MHMADYHYA/smart-neighborhood-power-system-design/docs/Stage_0_Understanding_Report.md

# Stage 0 — דוח הבנה וסיווג מקורות (סופי)
**תאריך:** 11/06/2026 · בוצע לפני תחילת העריכה, כנדרש.

## מהות הפרויקט
תיק תכנון סופי (אבן דרך רביעית — דוח מסכם) למערכת חשמל במתח נמוך לשכונת מגורים חכמה, מסווג **אפשרות ב׳** לפי הנחיות רשם המהנדסים: 3 בניינים (A/B/C) × 15 קומות (קרקע טכנית + 14 מגורים × 4 דירות) = **168 דירות** בחיבור 3×25A; הזנה 22kV דרך **2×1000kVA** (יבשים, Dyn11, uk≈6%) אל **MDB דו-מקטעי 2500A / Icw 65kA** (2×ACB 1600A + Bus-tie); **PV 200kWp**, **BESS 250kW/500kWh**, **30×11kW EV + DLM**, **גנרטור 300kVA + ATS**, **UPS 20kVA/8.75kWh**, **קבלים 200kvar detuned**, **EMS/BMS**, הארקת **TN-S**, חלוקה תת-קרקעית. ביקוש: 1,312.7 / 1,603.7kVA → העמסה 65.6% / 80.2%.

## קבצים שנמצאו, תפקידם ומה נעשה בהם
| קובץ / קבוצה | סיווג | שימוש |
|---|---|---|
| `Downloads\...מתוקן(2).docx` (11/06 13:11) | **דוח הבסיס** — תוכן אבן-דרך-3 לאחר תיקוני "סאלח" (574A, BESS Ir=380, ציבורי 23A/32A/4×10, AN, טבלת IEE) | מקור התוכן היחיד; חולץ ברמת בלוקים כולל משוואות OMML |
| `הנחיות משרד העבודה...23-02-2026.pdf` (+`_extracted\ministry.txt`) | דרישות מחייבות — רשם המהנדסים | בסיס טבלת ההתאמה (27 דרישות) בפרק 2 |
| `מדריך פרויקטים...04-26.pdf` (+`guide.txt`) | מגדיר את דרישות אבן הדרך הרביעית (דוח מסכם + שרטוטי חובה + פוסטר) | בסיס מיפוי הדרישות; הפוסטר מוגש בנפרד |
| `חוק החשמל 2017.pdf` | בסיס חוקי | סעיפי "התאמה לחוק" בכל פרק — עקרונות בלבד, ללא ציטוט מספרי סעיפים |
| IEC-60909.pdf, Electrodynamic forces, כוונון הגנות שניידר, קטלוגי Schneider/ABB/Eaton/Legrand, תקציר 4000 | מקורות טכניים/קטלוגיים | תיעוד בטבלת מקורות; ללא צילומי קטלוג בגוף הדוח (לפי ההנחיות) |
| `05_final_word\` + `_milestone3_build\` | תשתית בנייה קודמת (Word COM RTL, מחוללי שרטוטים) | אומצה והורחבה (build4, drawings_final) |
| `מקרא.dwg`, `תכנון לוחות חשמל.dwg`, `סכימת זרמי קצר+מפלי מתח.dwg` | קבצי AutoCAD מקוריים של הסטודנט | צורפו לחבילה (`_drawings_final\DWG_original`) ונרשמו בנספח L |
| `אמיר וסלאח.pdf`, `עודד ונמרוד.pdf`, תבניות אבן דרך, `אבן דרך שנייה.docx`, `11/222/3/4/5A.pdf` (הרצאות) | ייחוס סגנוני / רקע קורס | לא הועתק מהם תוכן |
| `01/02_*.txt` (פרומפטים ישנים), `_build\`, `CHANGELOG` | היסטוריית עבודה | לא בשימוש — הוחלפו בהנחיות הנוכחיות |

## סתירות וערכים ישנים שאותרו (ותוקנו)
1. **זהות** — הקובץ נשא ניסוחי "דוח ביניים – אבן דרך שלישית" בשער, בתקציר, בפרק 2, בפרק 20 ובעשרות פסקאות ("ראשוני", "יושלם בדוח הסופי").
2. **UPS הפוך** — במסמך 8.75kVA/20kWh; הנתון המחייב: **20kVA/8.75kWh** → חושבו מחדש מזין (MCB 40A, 4×10), Ik (3.4kA) וזמן גיבוי (≈1.1h).
3. **סתירה פנימית בפרק 9** — חישוב 9.1 השתמש ב-490A/MCCB 630/"2×5×240" מול 574A/800A/2×(4×300) בשאר הדוח.
4. **"4×35" שרד** בטבלת מפל המתח (רייזר) בסתירה ל-9.7 → מודל הרייזר תוקן ו-ΔU מצטבר עודכן 4.0%→3.5%.
5. **Icu של ACB** — 50kA בחלק מהטבלאות מול 65kA באחרות → אוחד ל-65/65kA.
6. **לוח קומה** — 125A/10kA/80A בלתי עקביים → אוחד ל-MCCB 80A, Icu 25kA.
7. **Ik ללוח ציבורי/UPS** (11/10kA) לא תאם לכבל 4×10 → חושב מחדש 3.4kA.
8. **שרטוטים ישנים** הציגו UPS 8.75kVA, PUBLIC 100A, 50kA → הופקו מחדש.
9. **חוסרים מול דרישות הדוח המסכם** — אין פרק חלופות, אין BOQ סופי, נספחים חלקיים (חסרים C/I/J/M), אין טבלאות התאמה מלאות, אין Ik,min לכל לוח, תהודת פסים "תושלם" — הכל הושלם.

## איך נבדקה ההתאמה לחוק החשמל ותקנות החשמל
לכל נושא תכן הוצגה שרשרת ההוכחה המעשית (Ib → In/Ir → Iz′ → I2≤1.45Iz′ → ΔU → Ik max/min → Icu/Ics → שיטת הגנה/הארקה → החלטה), בתוספת: טבלת התאמה לפי 16 נושאי תכנון (פרק 2), סעיף ייעודי בכל פרק הנדסי, ושתי טבלאות בקרה בפרק 22. בהיעדר ציטוט נוסח מחייב — הניסוח "בהתאם לעקרונות חוק החשמל ותקנות החשמל בנושא..." בלבד, ללא המצאת מספרי סעיפים.

## החלטת ביצוע
התוכן ההנדסי בבסיס נמצא איכותי ועקבי ברובו; הביצוע התמקד ב: (א) הסבת הזהות לדוח מסכם; (ב) השלמת הפרקים/נספחים/טבלאות הנדרשים; (ג) תיקון הסתירות שלעיל; (ד) הפקת שרטוטים סופיים תואמי-ערכים והטמעתם; (ה) בקרת איכות ממוכנת. כל המספרים הקבועים של הפרויקט נשמרו ללא שינוי.
