MHMADYHYA/smart-neighborhood-power-system-design/docs/source_manifest.md

# Source Manifest

- Local source: `C:\Users\mhmad\OneDrive\Desktop\סוף כנרת_final_submission\דוח מסכם - אבן דרך רביעית - תכנון שכונת מגורים חכמה - סופי.docx`

Raw reports with student IDs or private information were intentionally not copied into this public-ready repository.
