MHMADYHYA/smart-neighborhood-power-system-design/assets/full_report_media/report_media_002.png

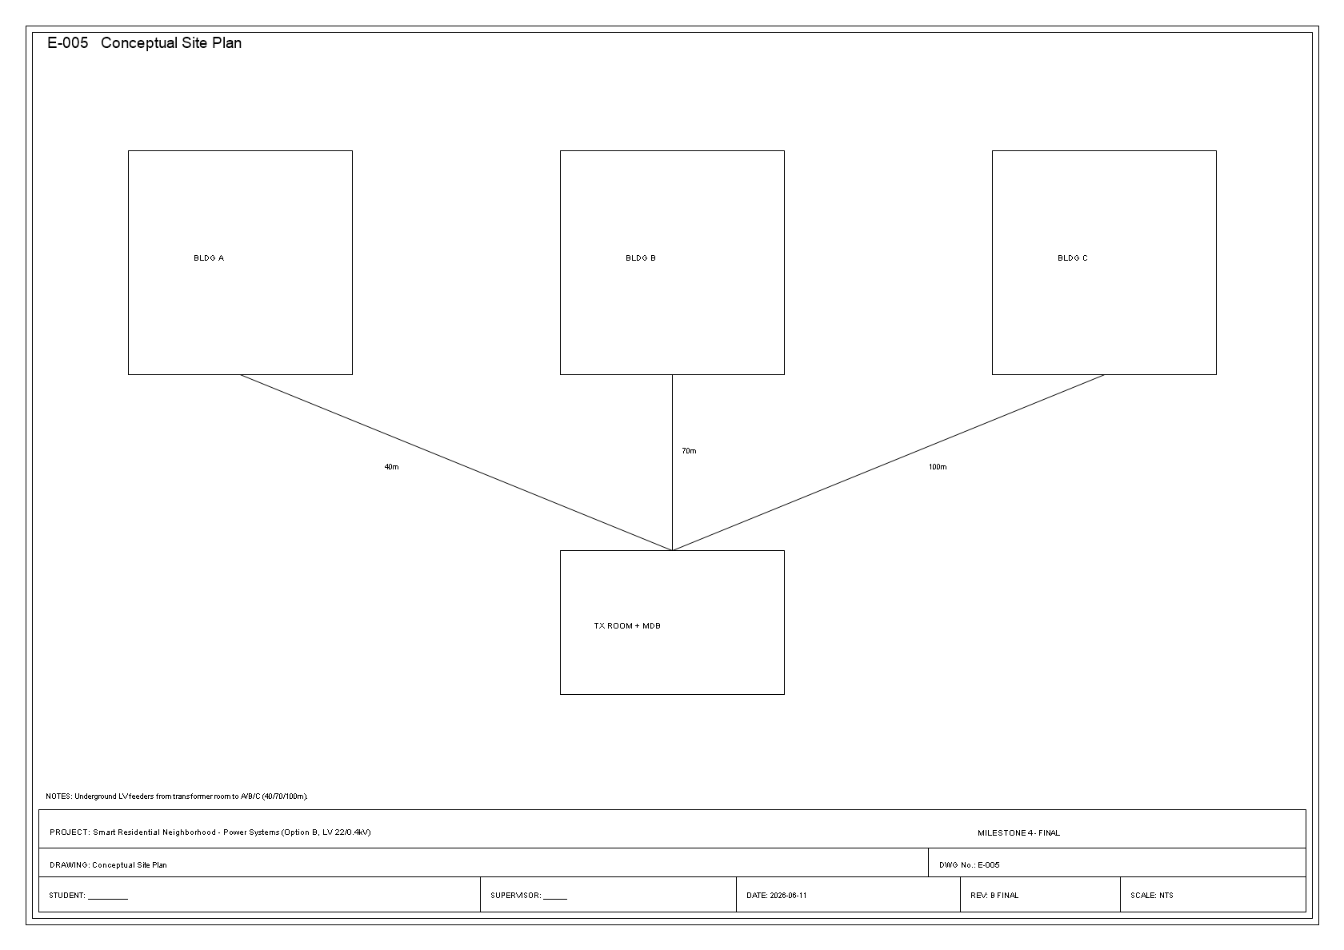
assets/full_report_media/report_media_002.png
