MHMADYHYA/smart-neighborhood-power-system-design/assets/rendered_report_pages/דוח_מסכם_-_אבן_דרך_רביעית_-_תכנון_שכונת_מגורים_חכמה_-_סופי-004.png

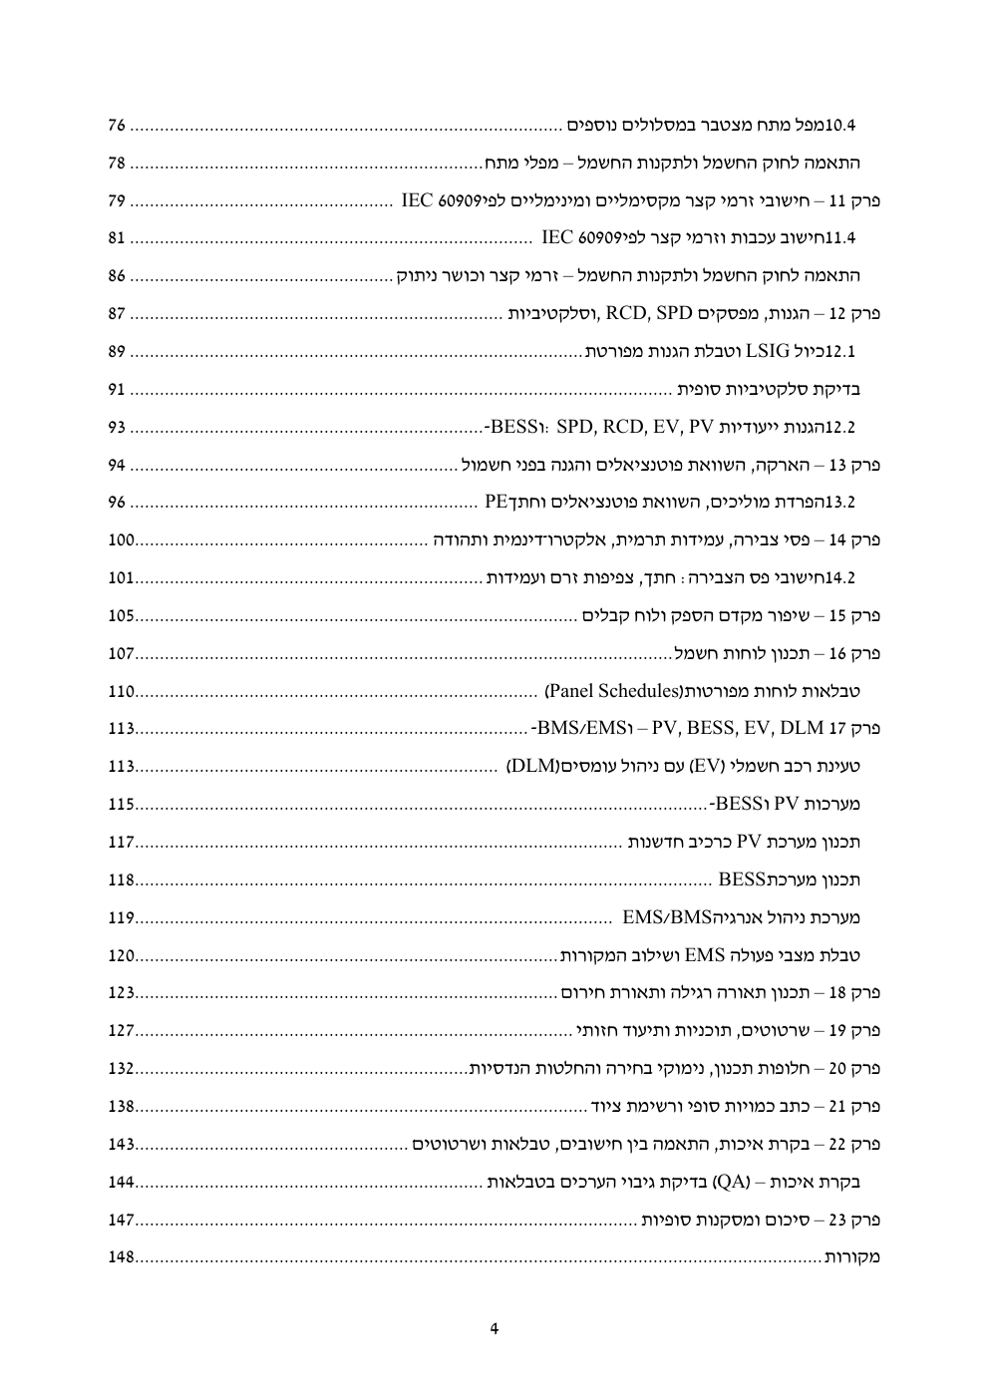
assets/rendered_report_pages/דוח_מסכם_-_אבן_דרך_רביעית_-_תכנון_שכונת_מגורים_חכמה_-_סופי-004.png
