MHMADYHYA/smart-neighborhood-power-system-design/engineering_drawings/E-001_Main_SLD_Neighborhood.png

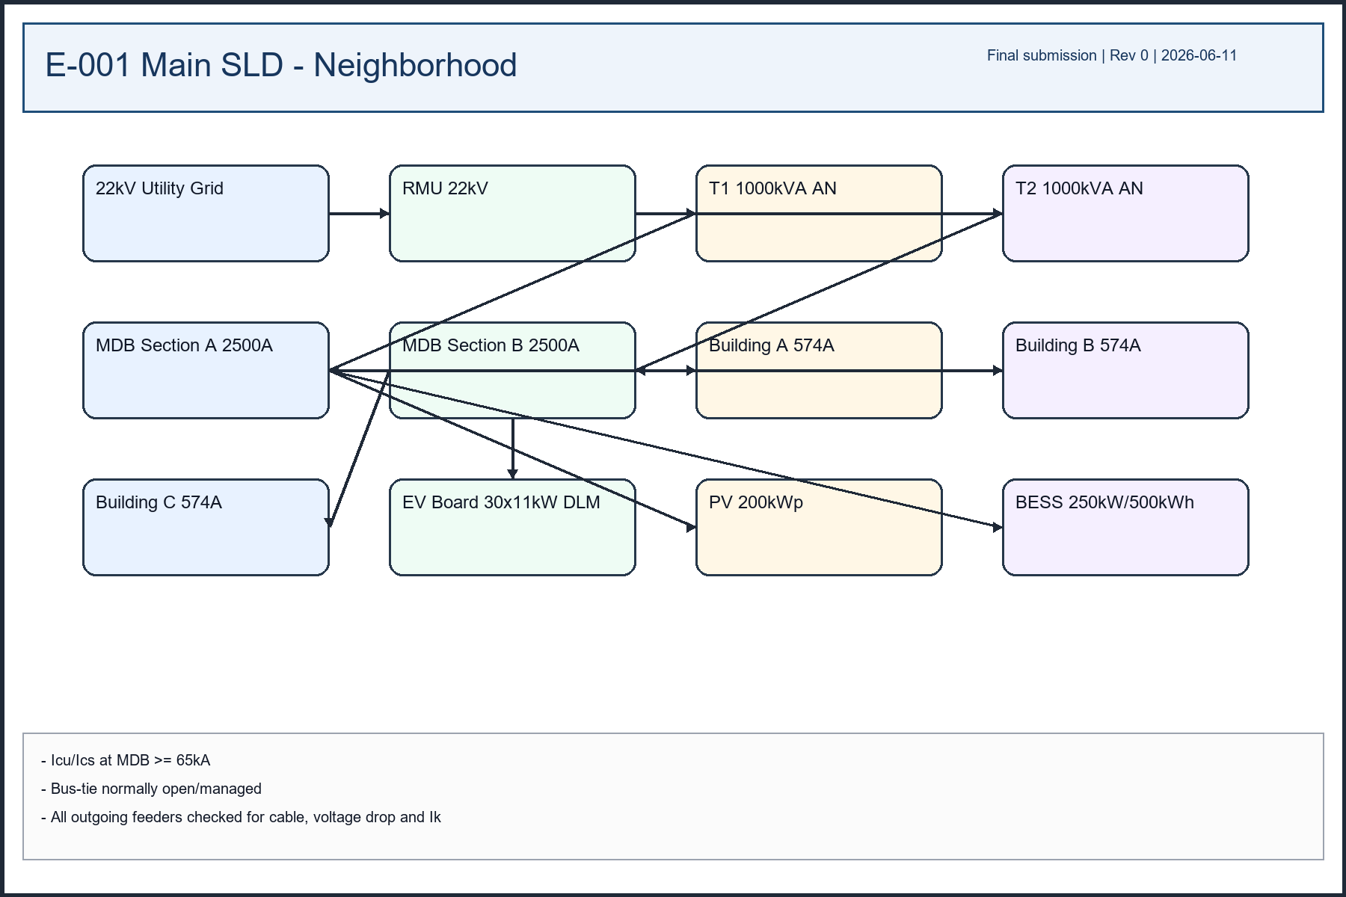
engineering_drawings/E-001_Main_SLD_Neighborhood.png
