MHMADYHYA/smart-neighborhood-power-system-design/engineering_drawings/E-004_Sub_Panels_Layout.png

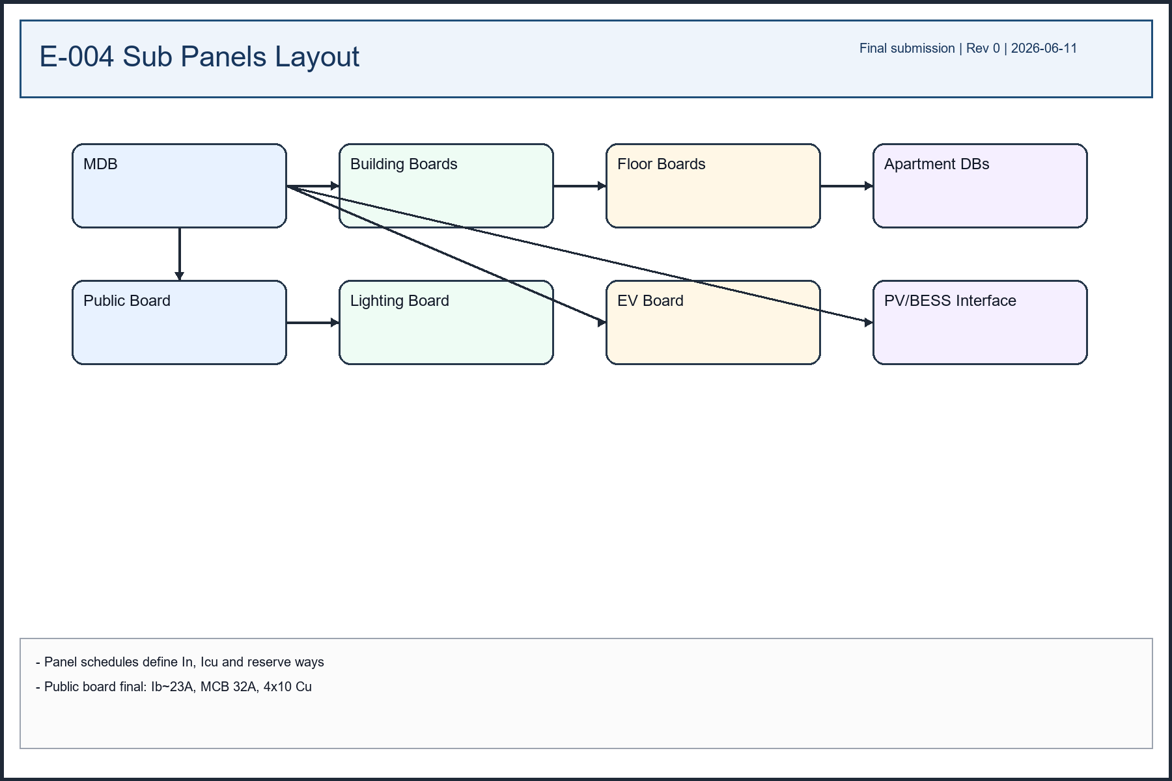
engineering_drawings/E-004_Sub_Panels_Layout.png
