MHMADYHYA/smart-neighborhood-power-system-design/engineering_drawings/E-005_Conceptual_Site_Plan.png

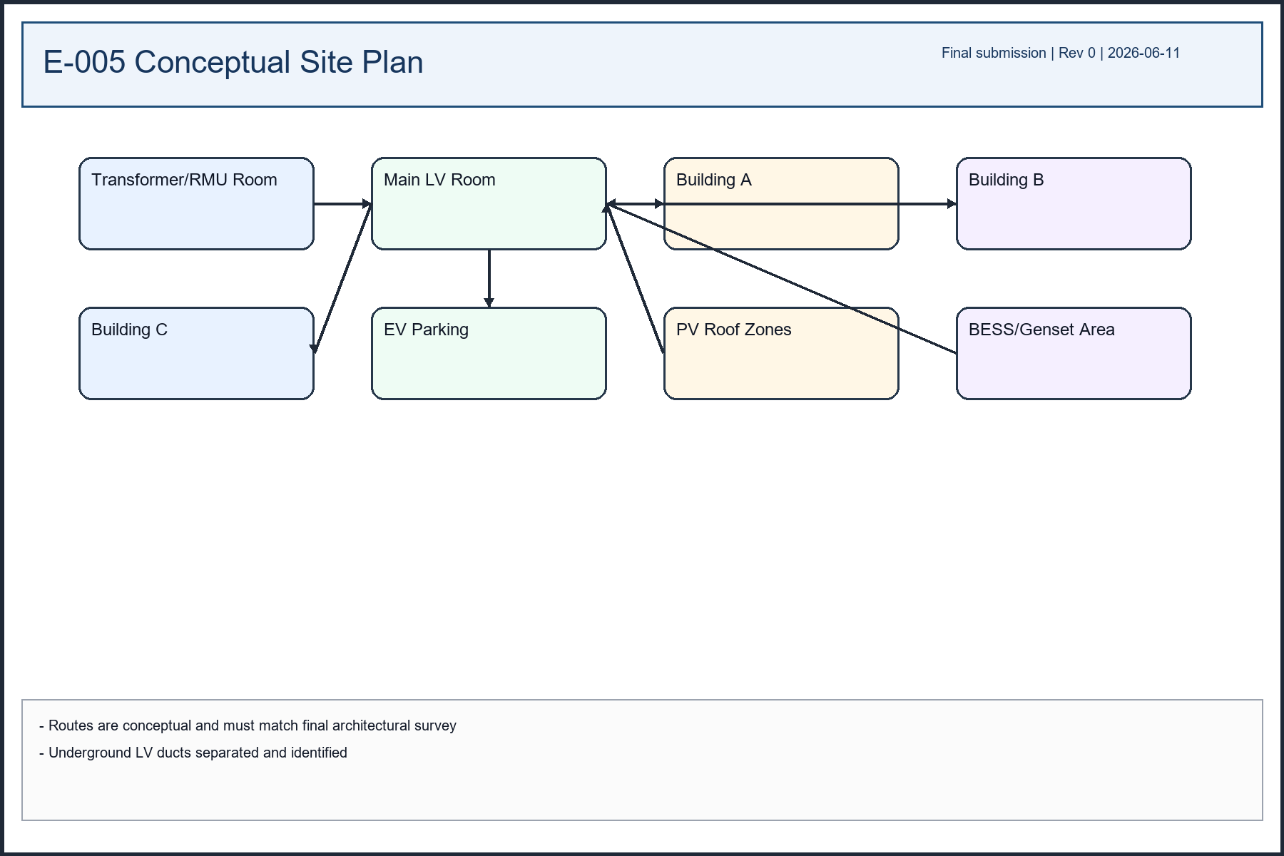
engineering_drawings/E-005_Conceptual_Site_Plan.png
