MHMADYHYA/smart-neighborhood-power-system-design/engineering_drawings/E-006_Underground_Cable_Routing.png

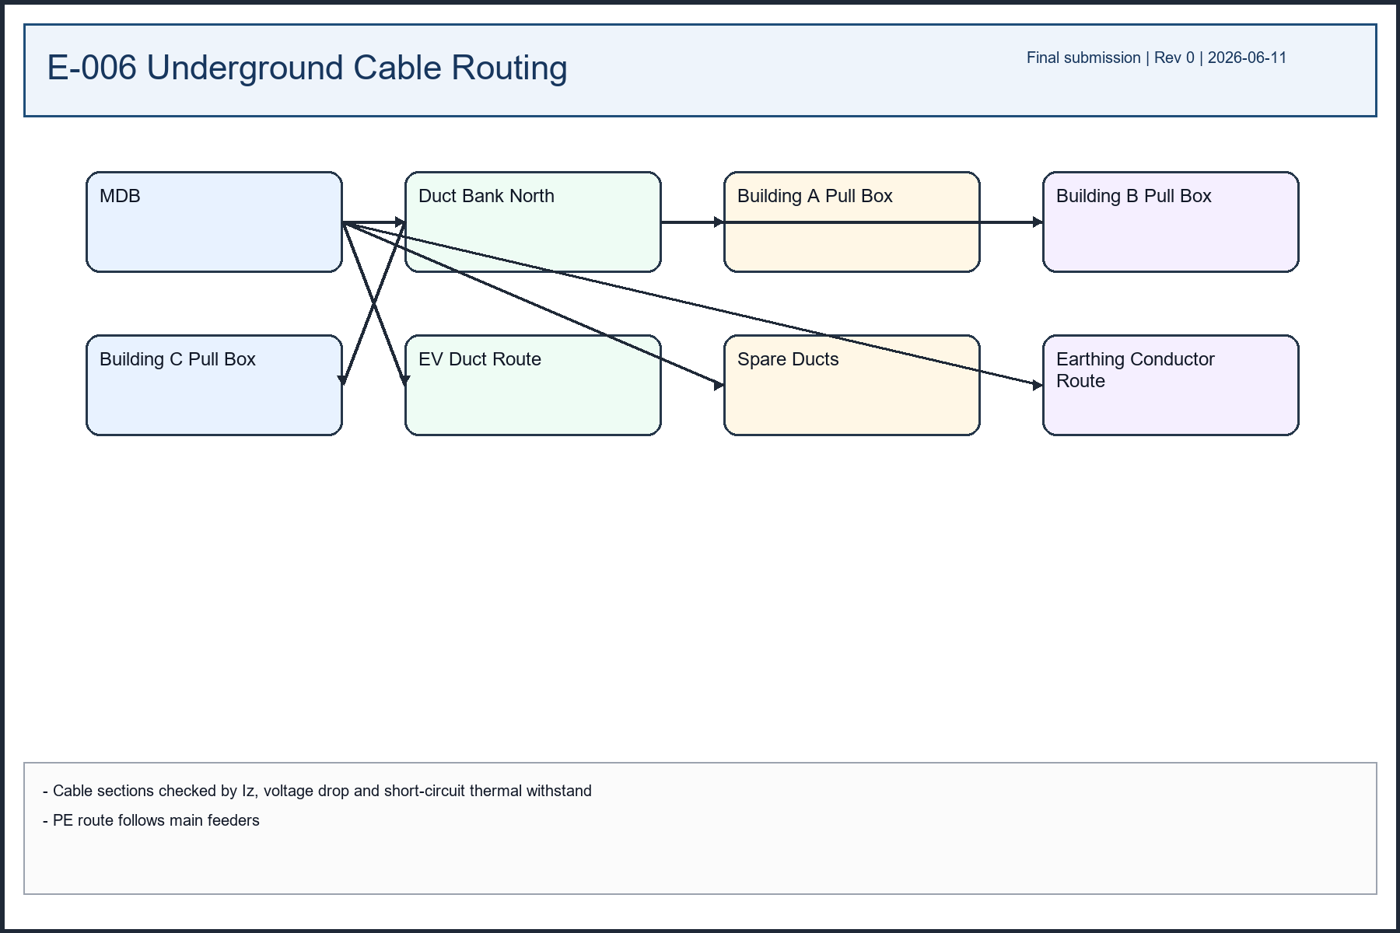
engineering_drawings/E-006_Underground_Cable_Routing.png
