MHMADYHYA/smart-neighborhood-power-system-design/engineering_drawings/E-007_Transformer_RMU_Room.png

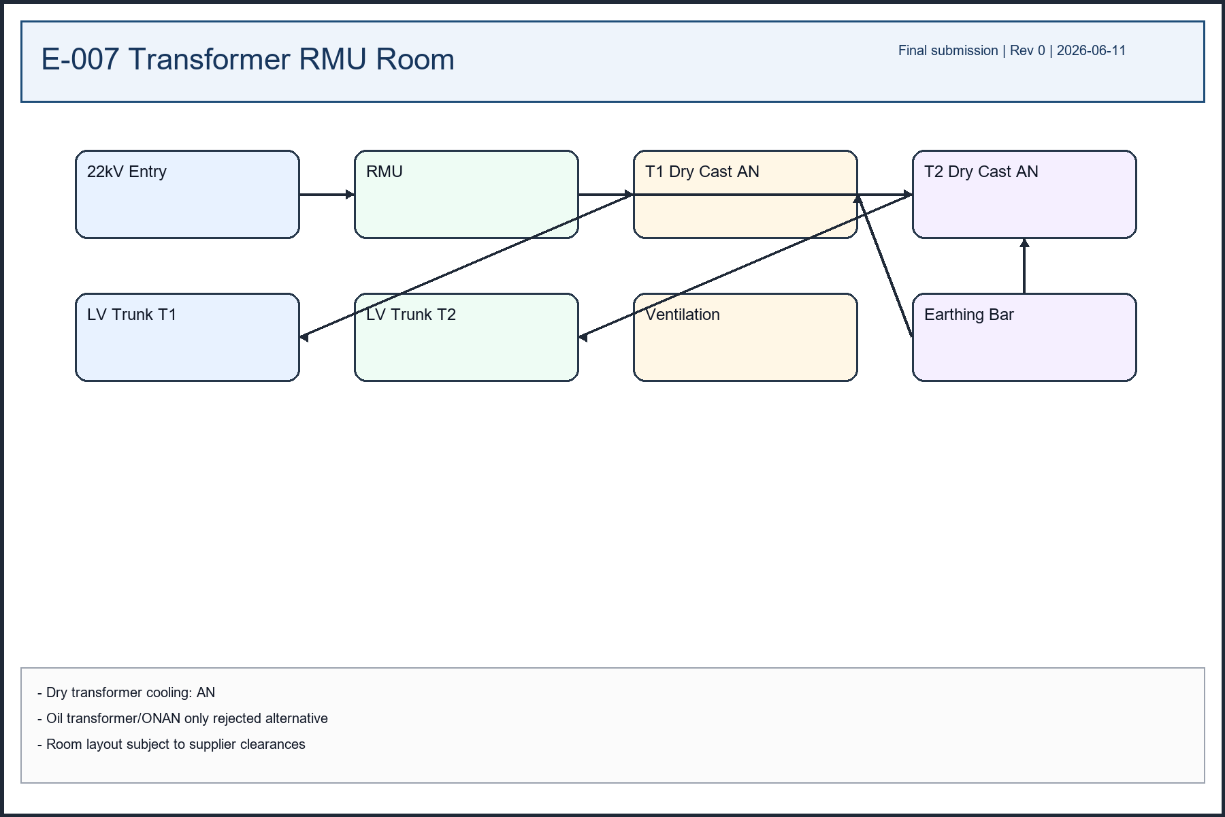
engineering_drawings/E-007_Transformer_RMU_Room.png
