MHMADYHYA/smart-neighborhood-power-system-design/engineering_drawings/E-008_Generator_ATS_UPS_SLD.png

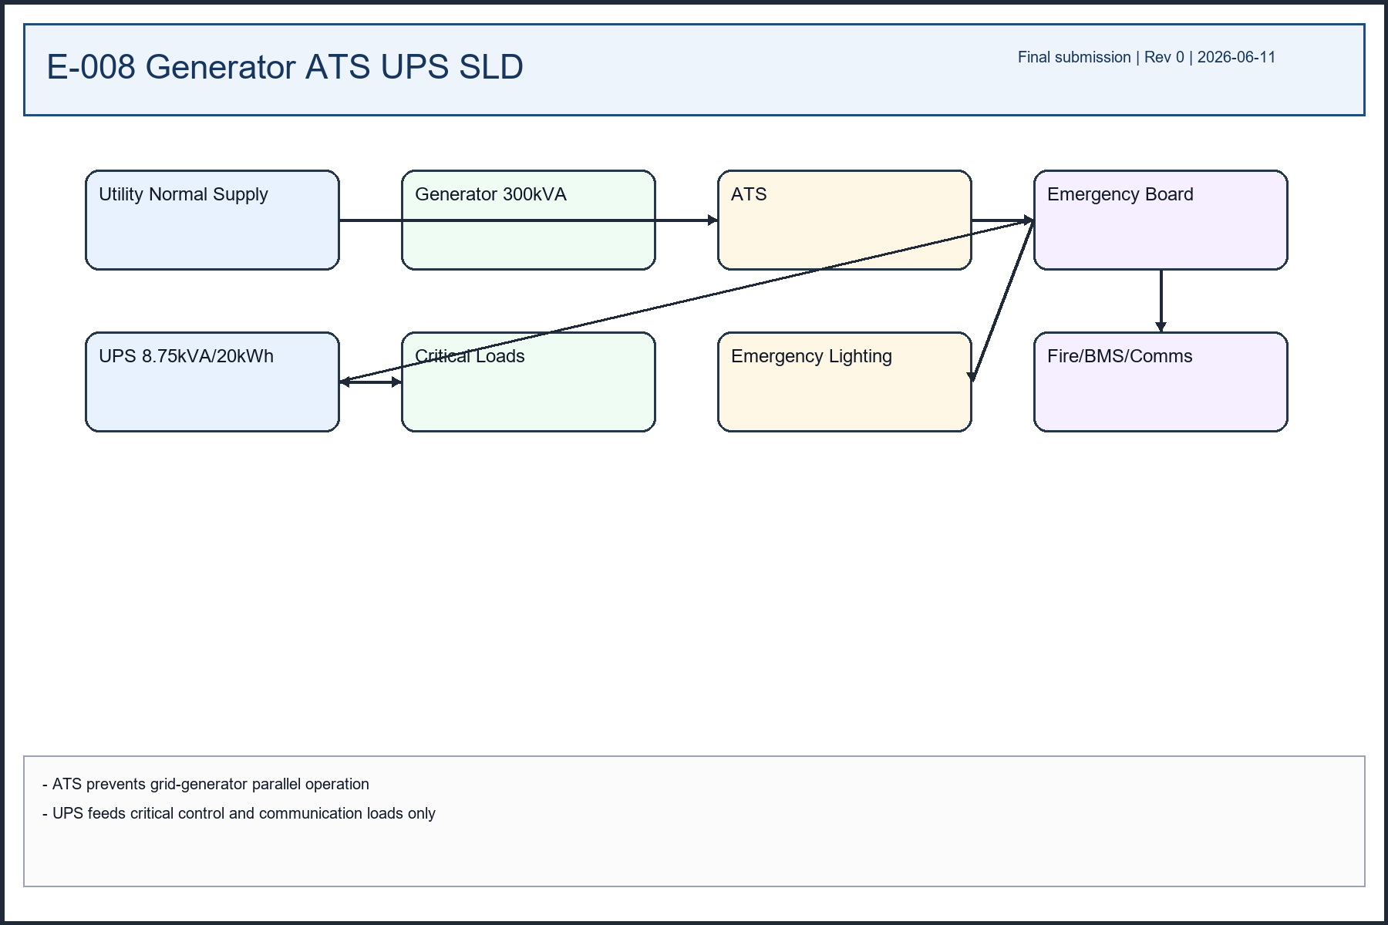
engineering_drawings/E-008_Generator_ATS_UPS_SLD.png
