MHMADYHYA/smart-neighborhood-power-system-design/engineering_drawings/E-009_PV_BESS_EV_SLD.png

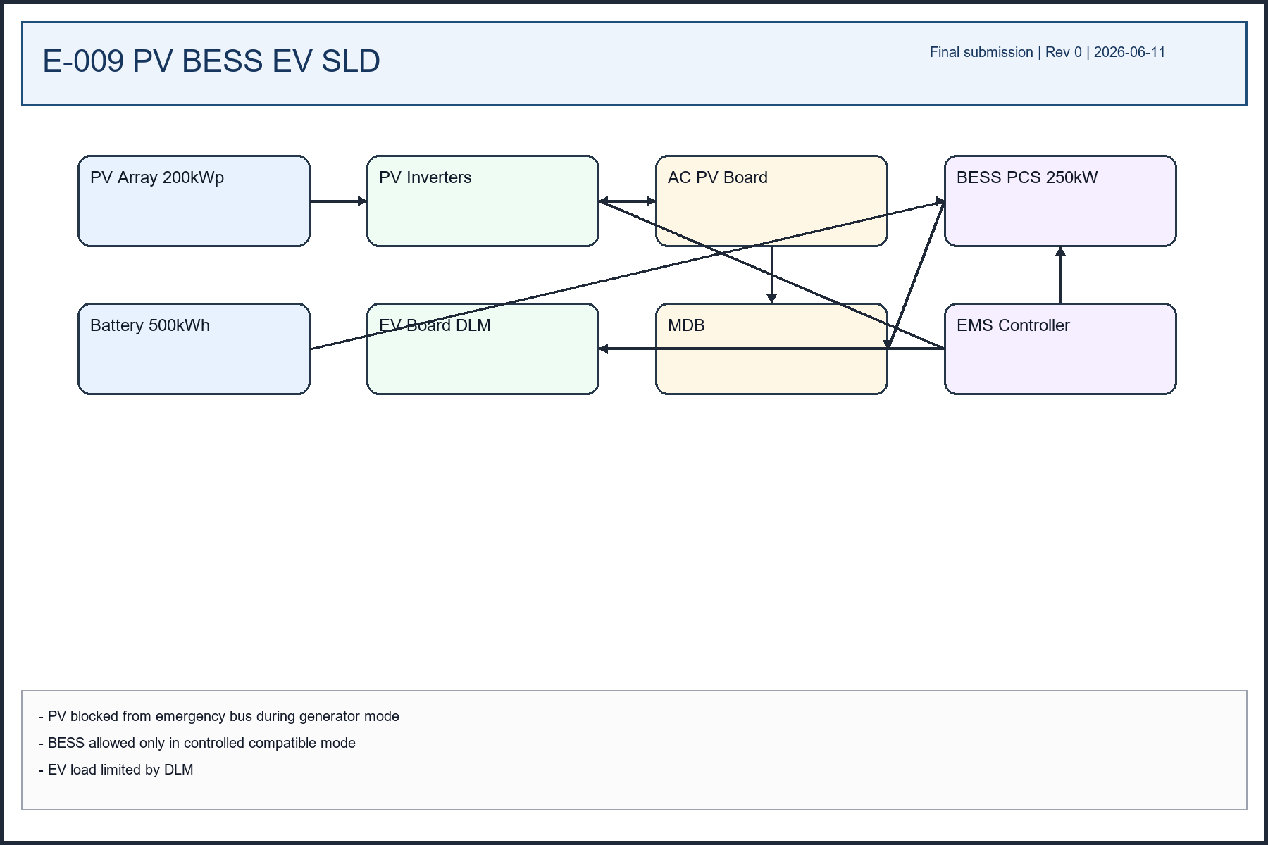
engineering_drawings/E-009_PV_BESS_EV_SLD.png
