MHMADYHYA/smart-neighborhood-power-system-design/engineering_drawings/E-010_Earthing_and_Bonding.png

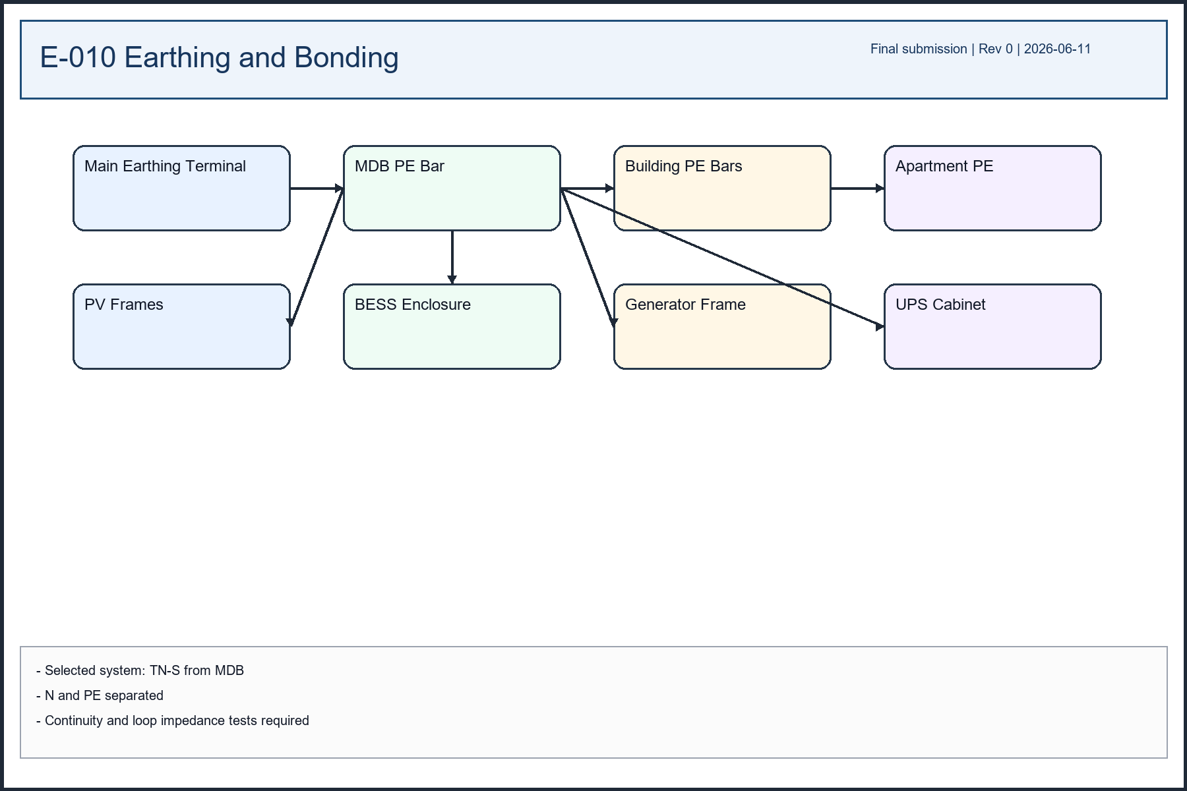
engineering_drawings/E-010_Earthing_and_Bonding.png
