MHMADYHYA/smart-neighborhood-power-system-design/engineering_drawings/E-011_Protection_Selectivity.png

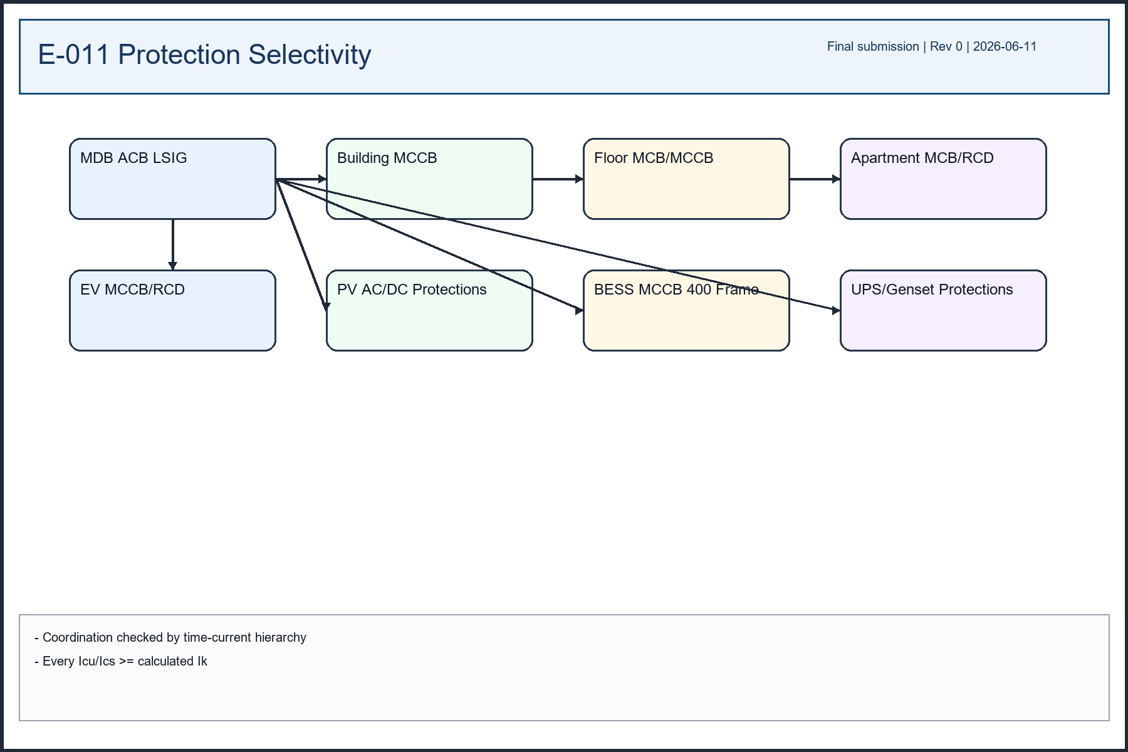
engineering_drawings/E-011_Protection_Selectivity.png
