MHMADYHYA/smart-neighborhood-power-system-design/engineering_drawings/E-012_BMS_EMS_Architecture.png

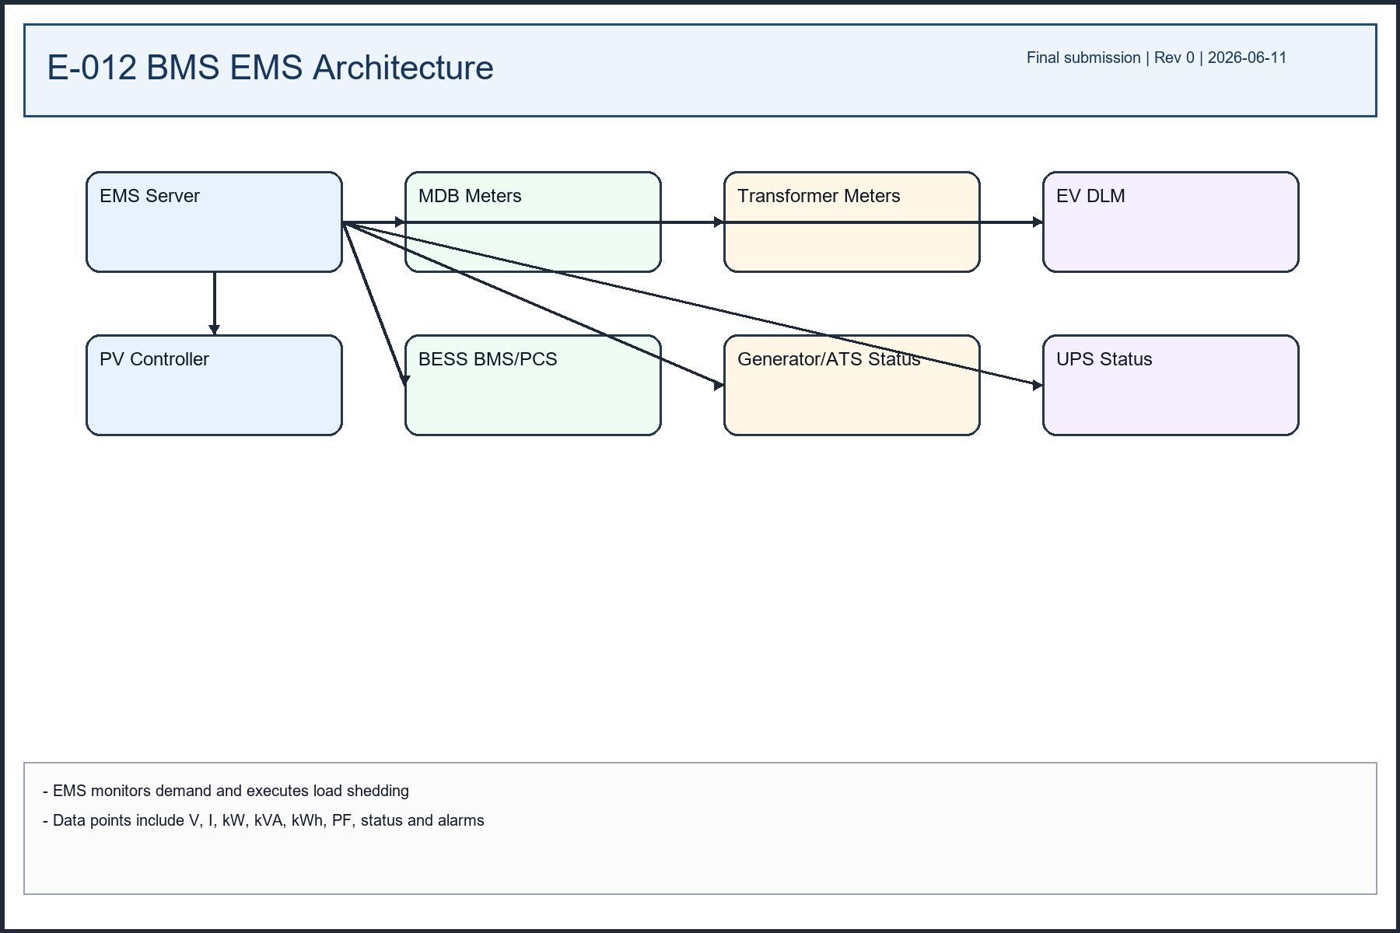
engineering_drawings/E-012_BMS_EMS_Architecture.png
