MHMADYHYA/smart-neighborhood-power-system-design/engineering_drawings/E-013_Lighting_and_Emergency_Lighting.png

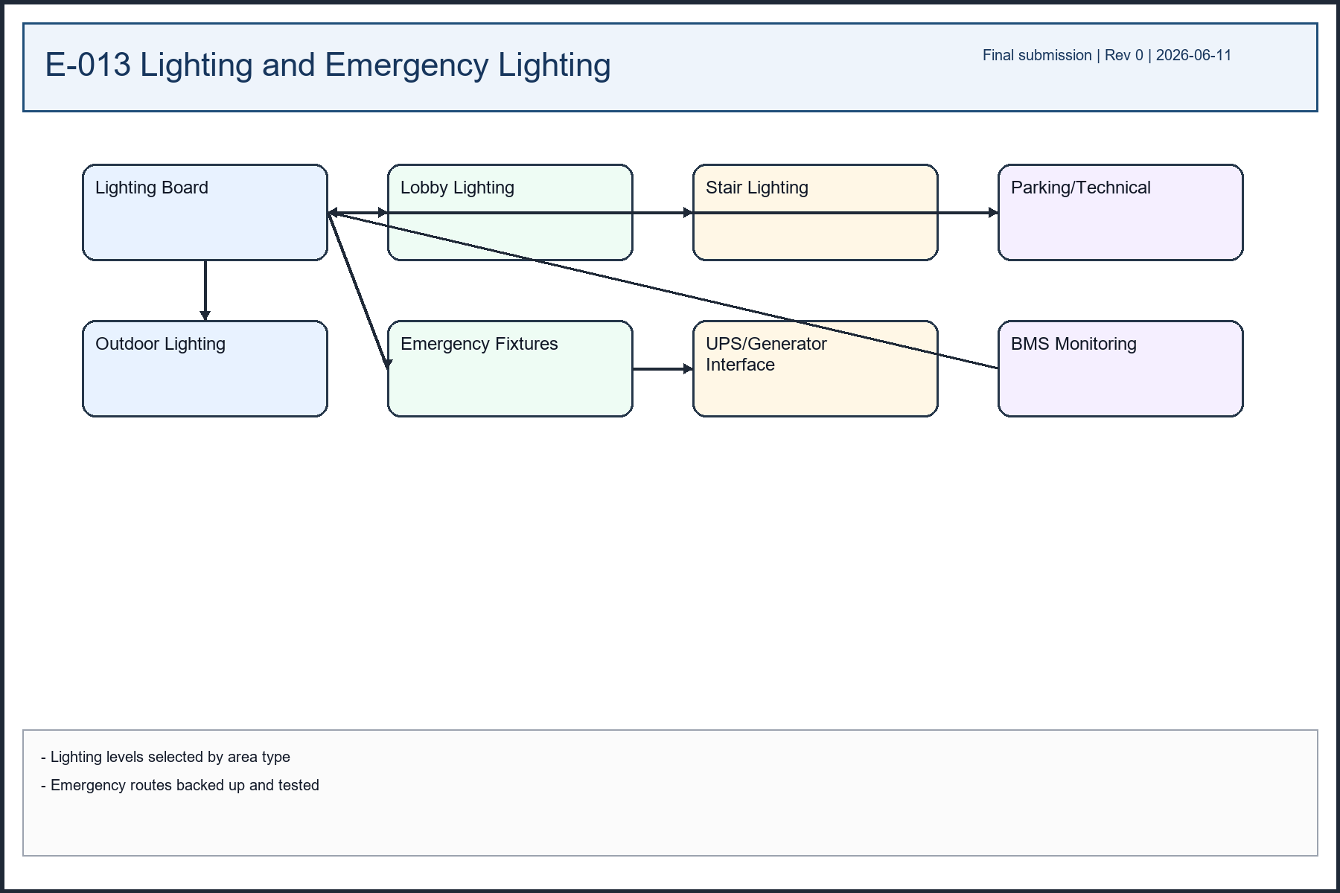
engineering_drawings/E-013_Lighting_and_Emergency_Lighting.png
