MHMADYHYA/smart-neighborhood-power-system-design/engineering_drawings/E-014_Final_Coordination_Drawing.png

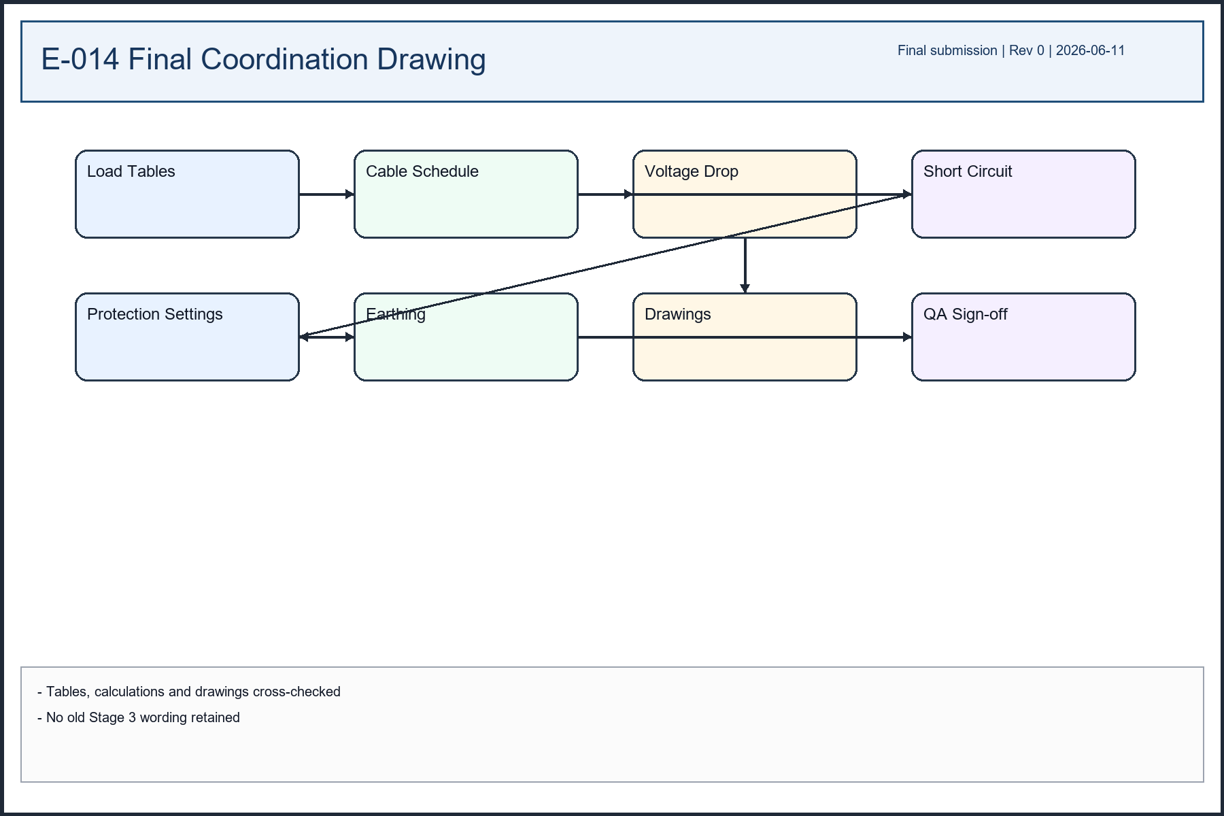
engineering_drawings/E-014_Final_Coordination_Drawing.png
