MHMADYHYA/smart-neighborhood-power-system-design/engineering_drawings/E-015_Normal_LV_Distribution_View.png

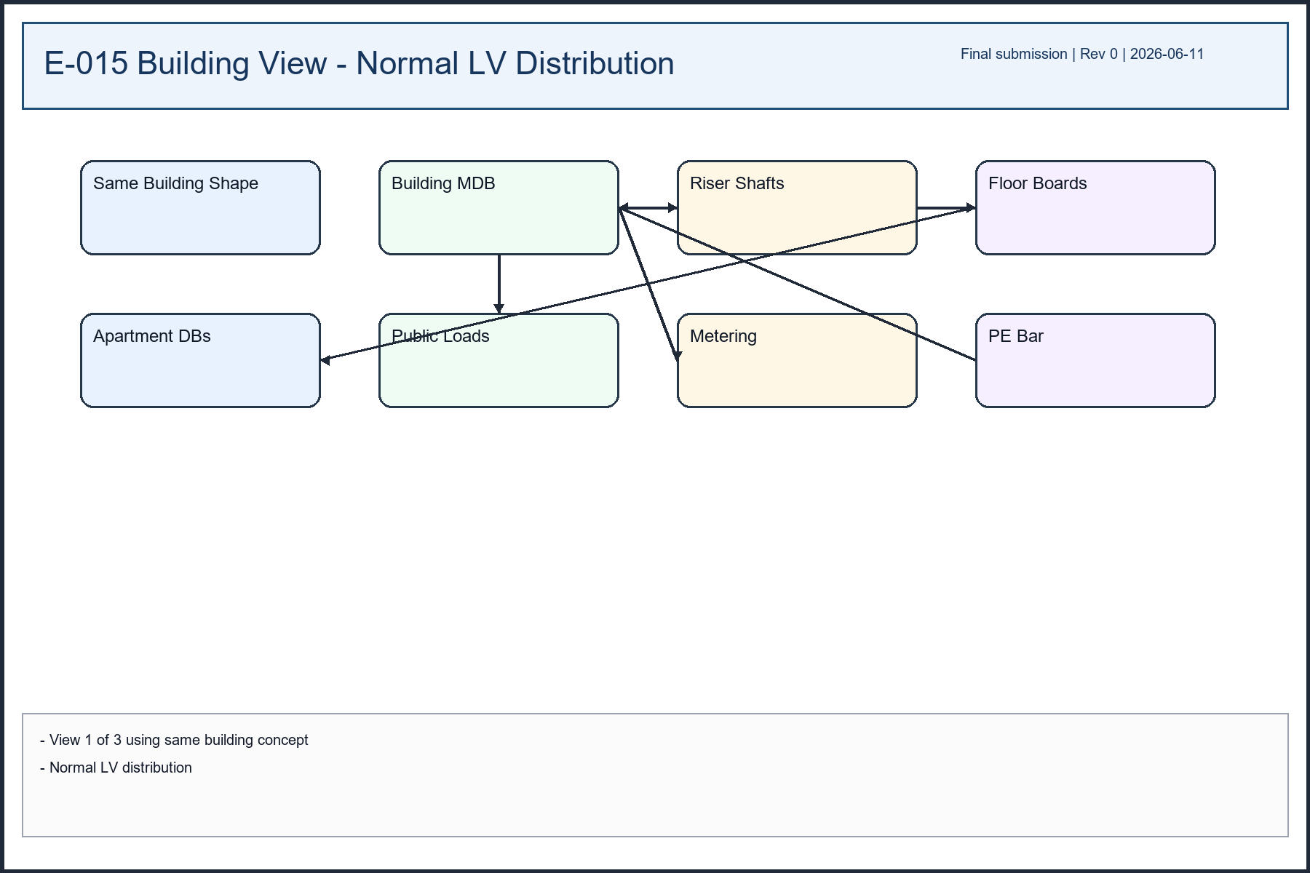
engineering_drawings/E-015_Normal_LV_Distribution_View.png
