MHMADYHYA/smart-neighborhood-power-system-design/engineering_drawings/E-017_Earthing_Bonding_View.png

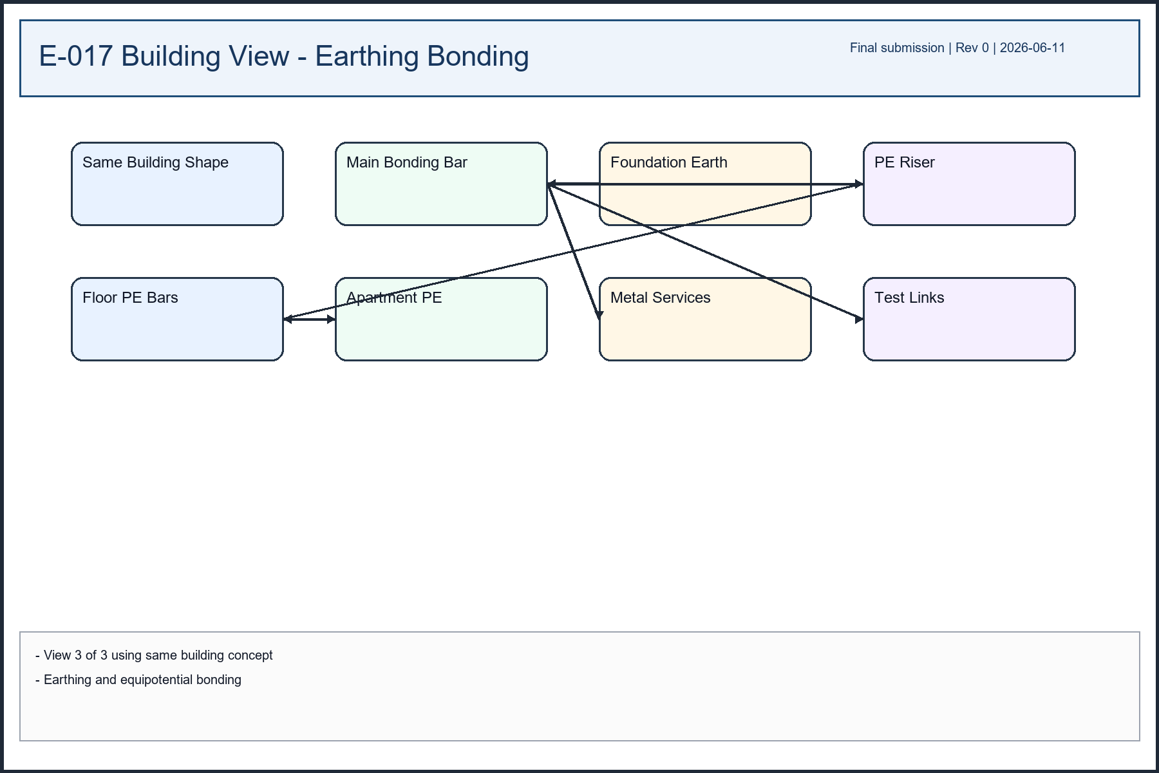
engineering_drawings/E-017_Earthing_Bonding_View.png
