MHMADYHYA/smart-neighborhood-power-system-design/engineering_drawings/PNG/E-003_Main_LV_MDB_Layout.png

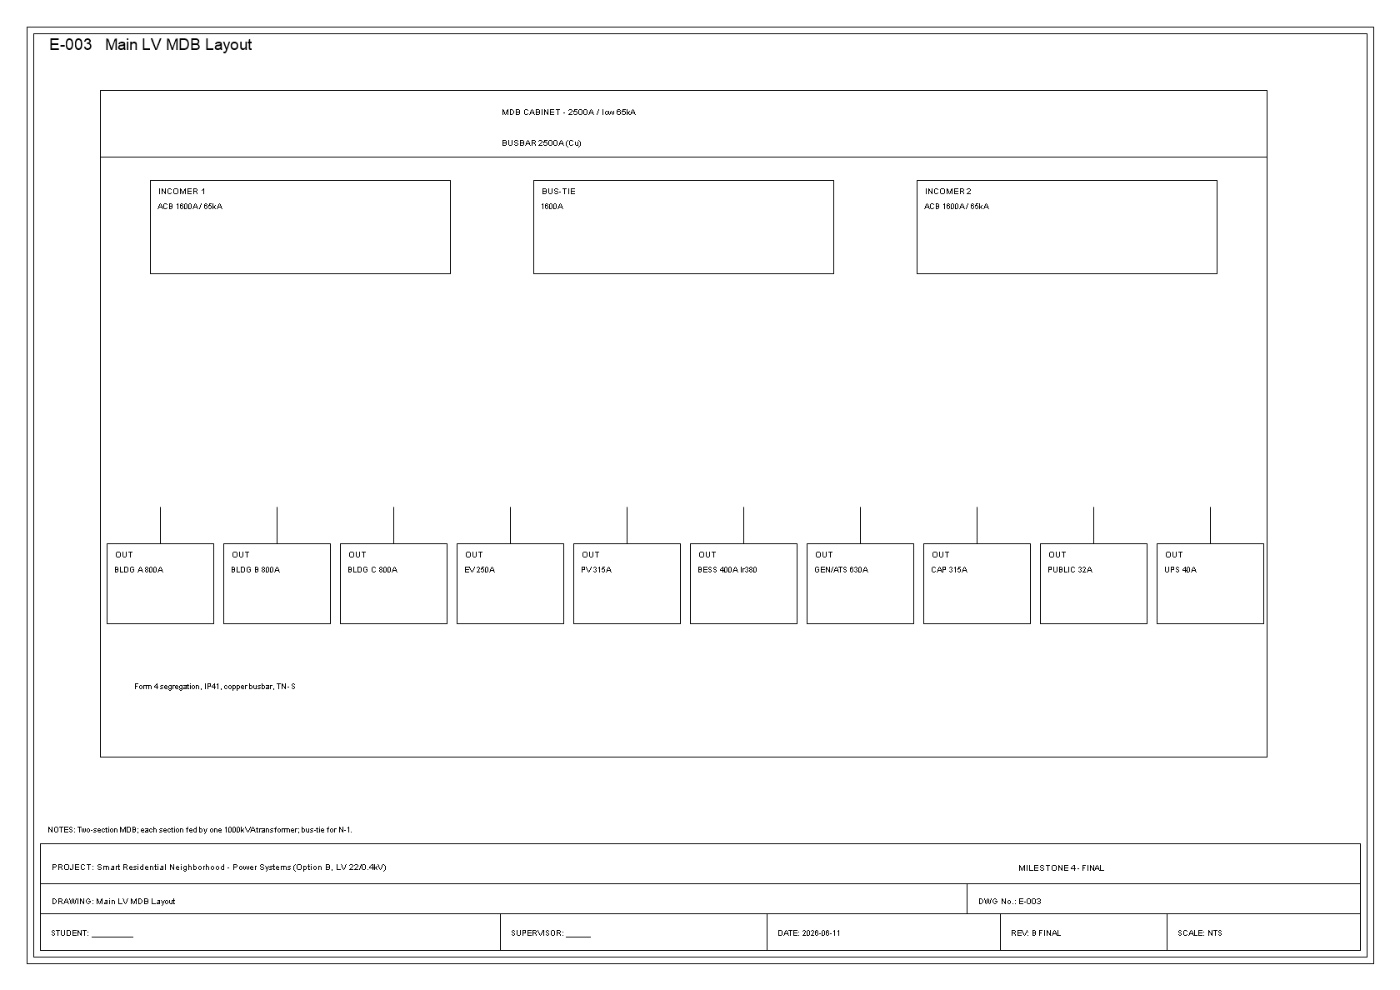
engineering_drawings/PNG/E-003_Main_LV_MDB_Layout.png
