MHMADYHYA/smart-neighborhood-power-system-design/engineering_drawings/PNG/E-006_Underground_Cable_Routes.png

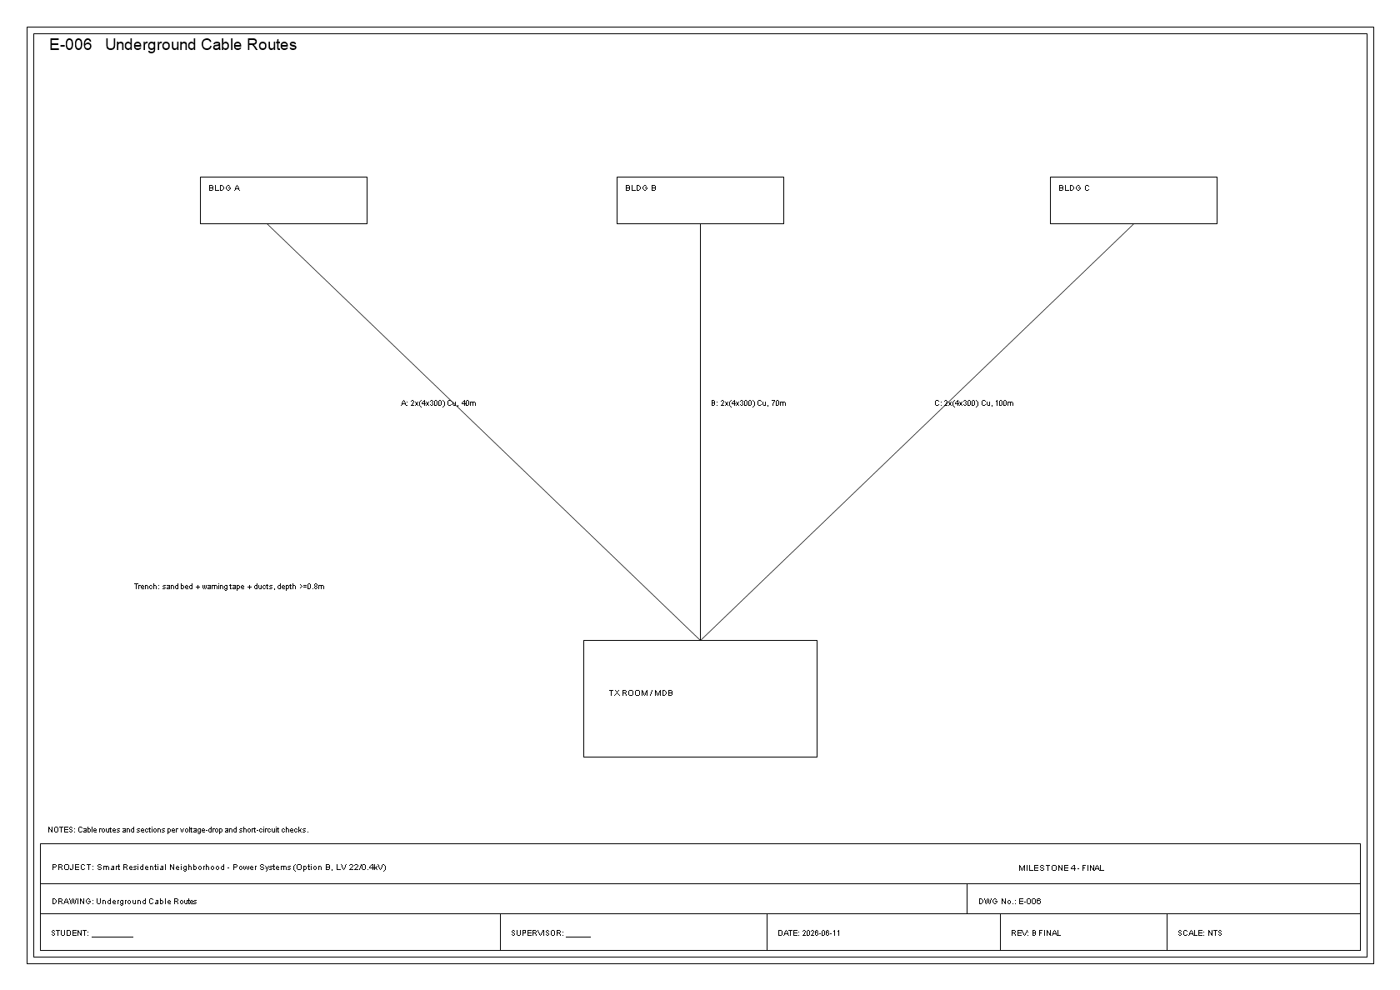
engineering_drawings/PNG/E-006_Underground_Cable_Routes.png
