MHMADYHYA/smart-neighborhood-power-system-design/engineering_drawings/PNG/E-007_Transformer_Room_Layout.png

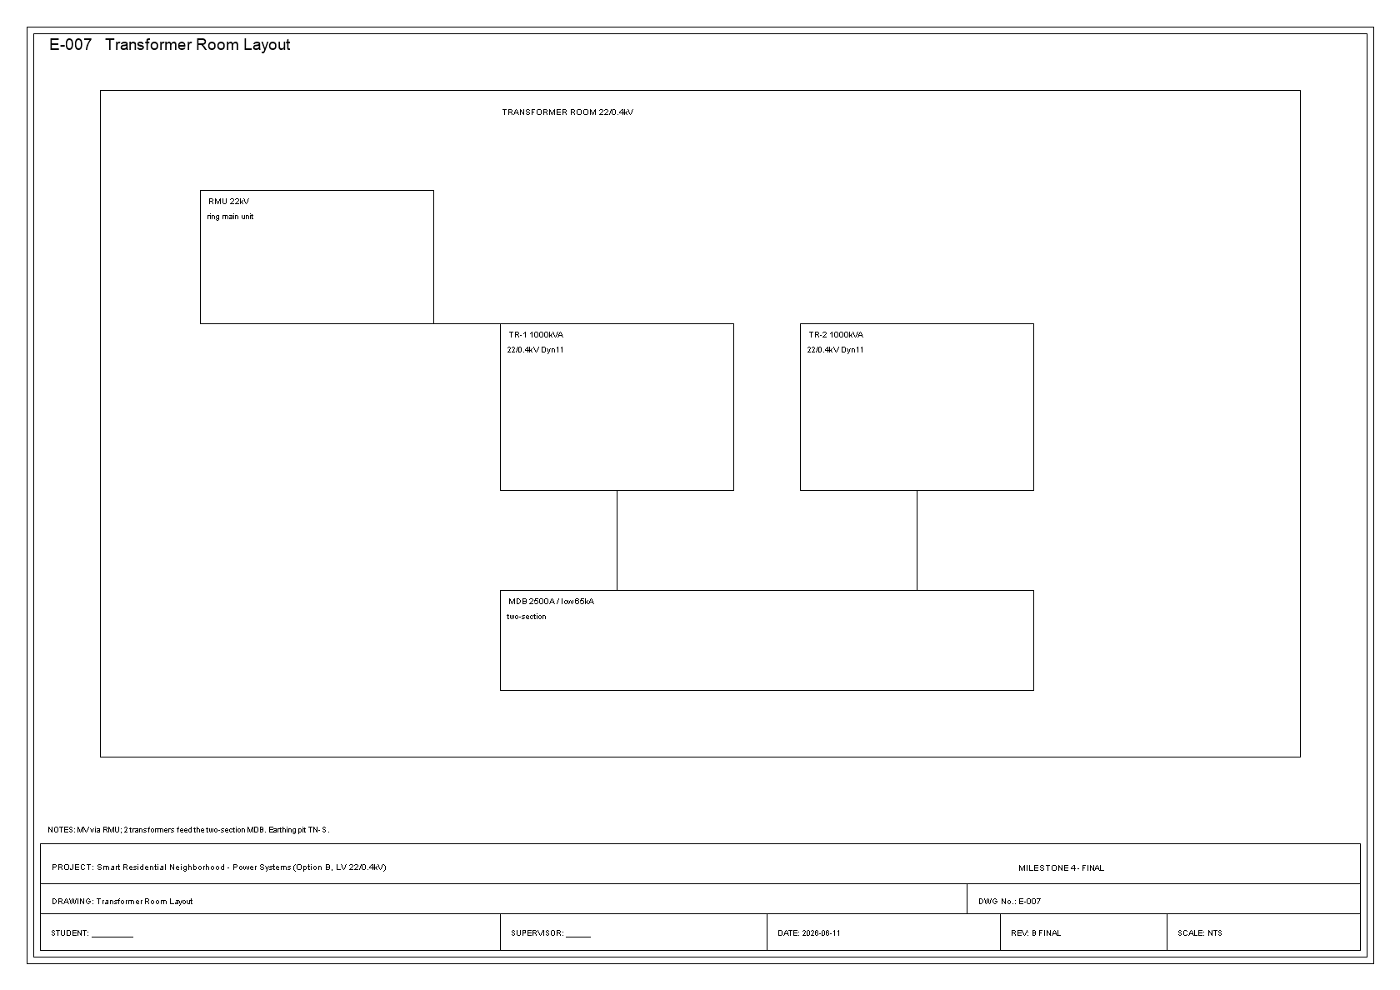
engineering_drawings/PNG/E-007_Transformer_Room_Layout.png
