MHMADYHYA/smart-neighborhood-power-system-design/engineering_drawings/PNG/E-012_EMS_BMS_Architecture.png

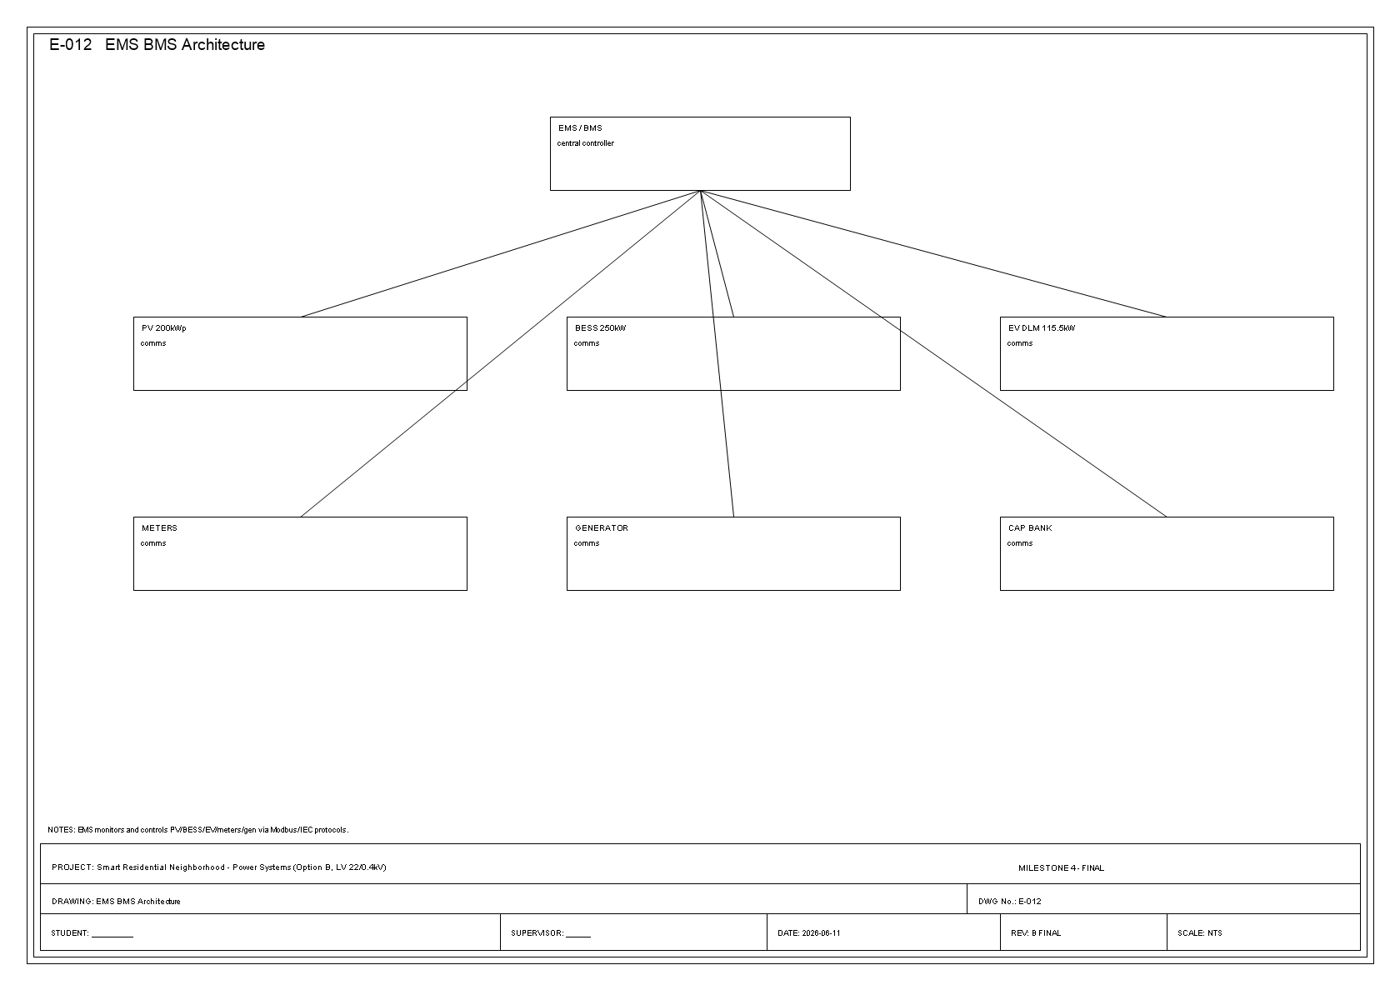
engineering_drawings/PNG/E-012_EMS_BMS_Architecture.png
