MHMADYHYA/smart-neighborhood-power-system-design/engineering_drawings/PNG/E-013_Lighting_Emergency_Lighting.png

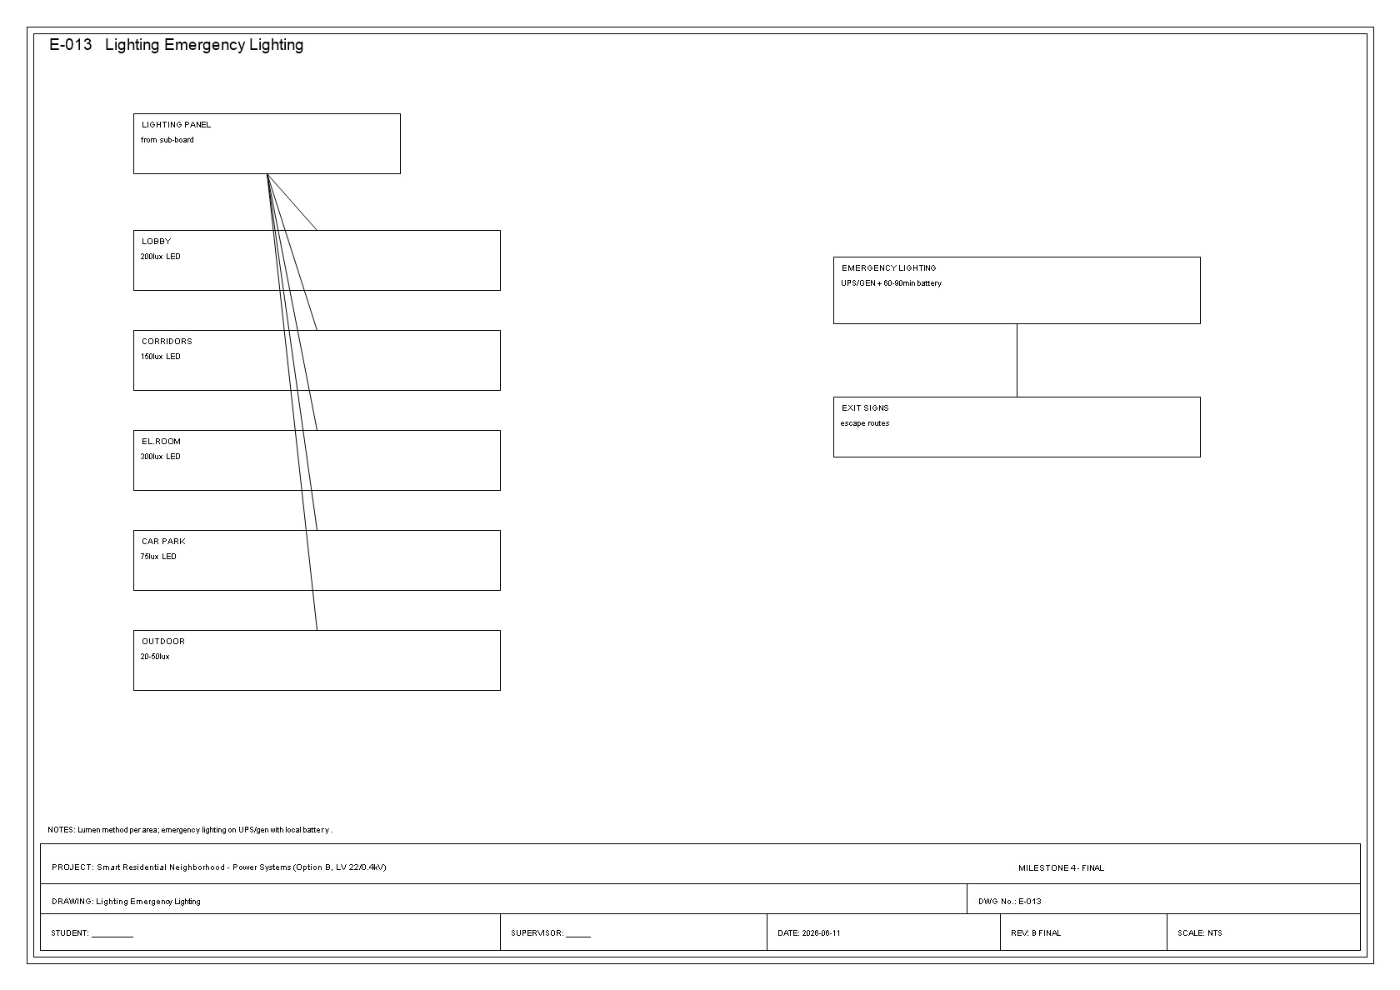
engineering_drawings/PNG/E-013_Lighting_Emergency_Lighting.png
