MHMADYHYA/smart-neighborhood-power-system-design/engineering_drawings/PNG/E-014_Overall_System_Overview.png

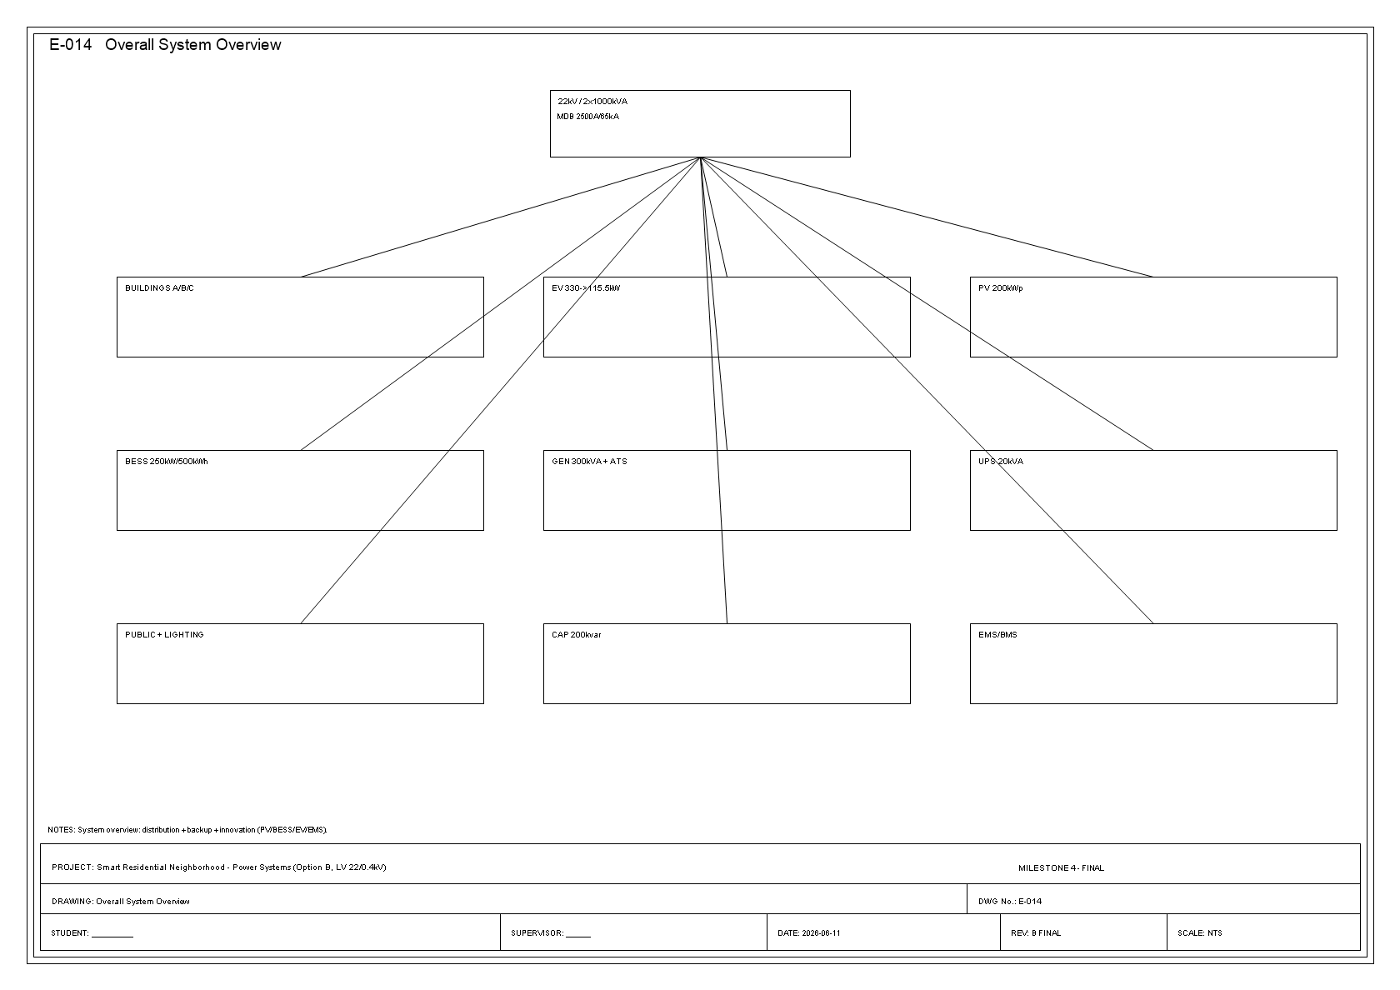
engineering_drawings/PNG/E-014_Overall_System_Overview.png
