MHMADYHYA/smart-neighborhood-power-system-design/engineering_drawings/PNG/E-015_EV_Charging_Detailed_SLD.png

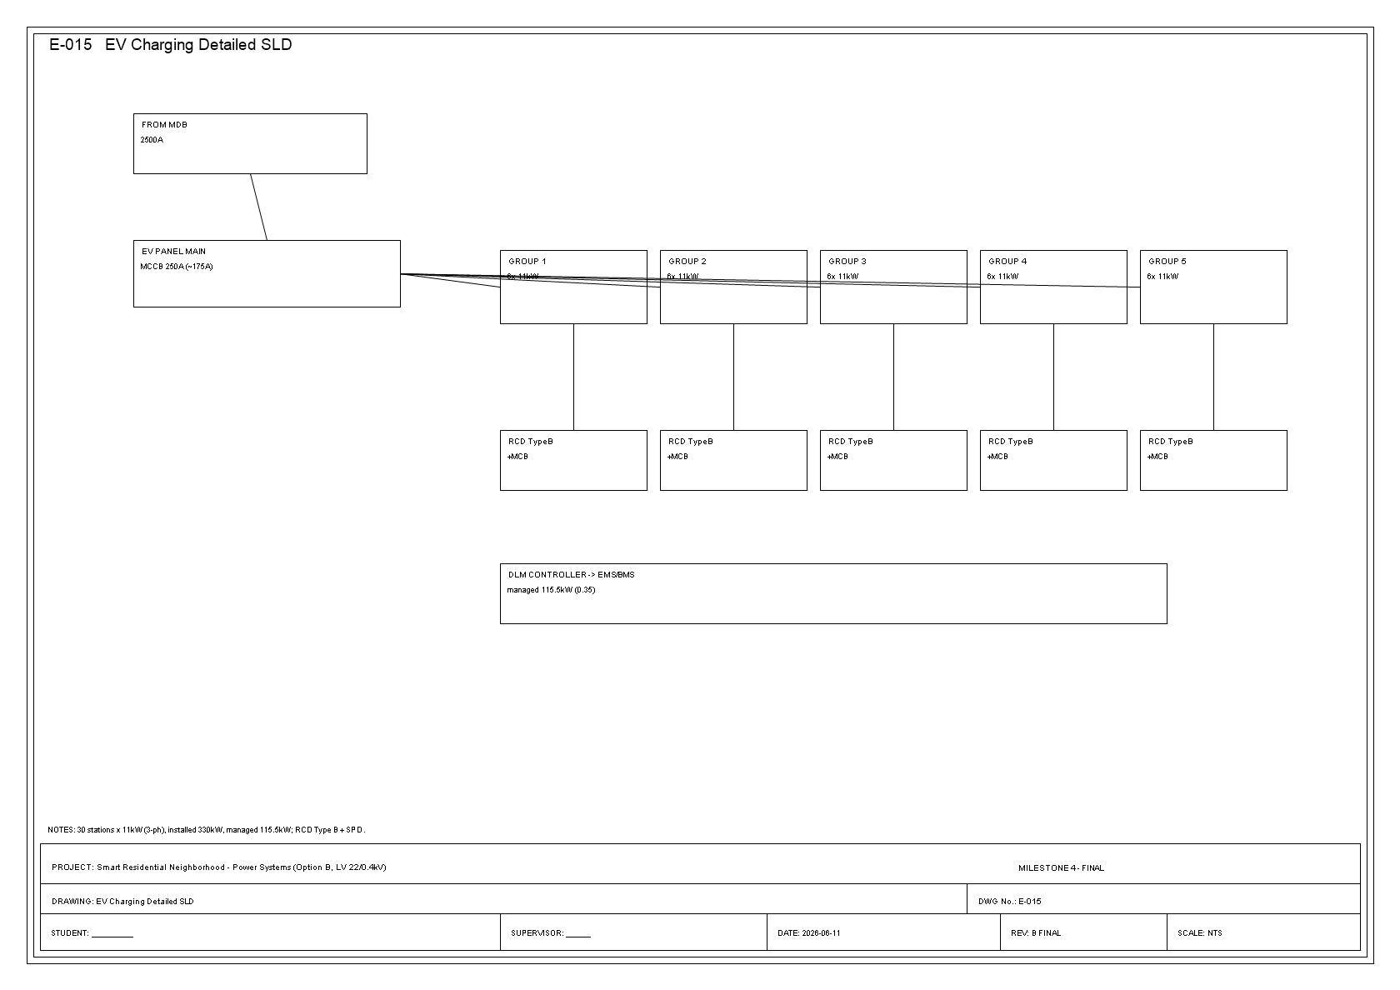
engineering_drawings/PNG/E-015_EV_Charging_Detailed_SLD.png
