MHMADYHYA/smart-neighborhood-power-system-design/engineering_drawings/PNG/E-016_PV_BESS_Detailed_SLD.png

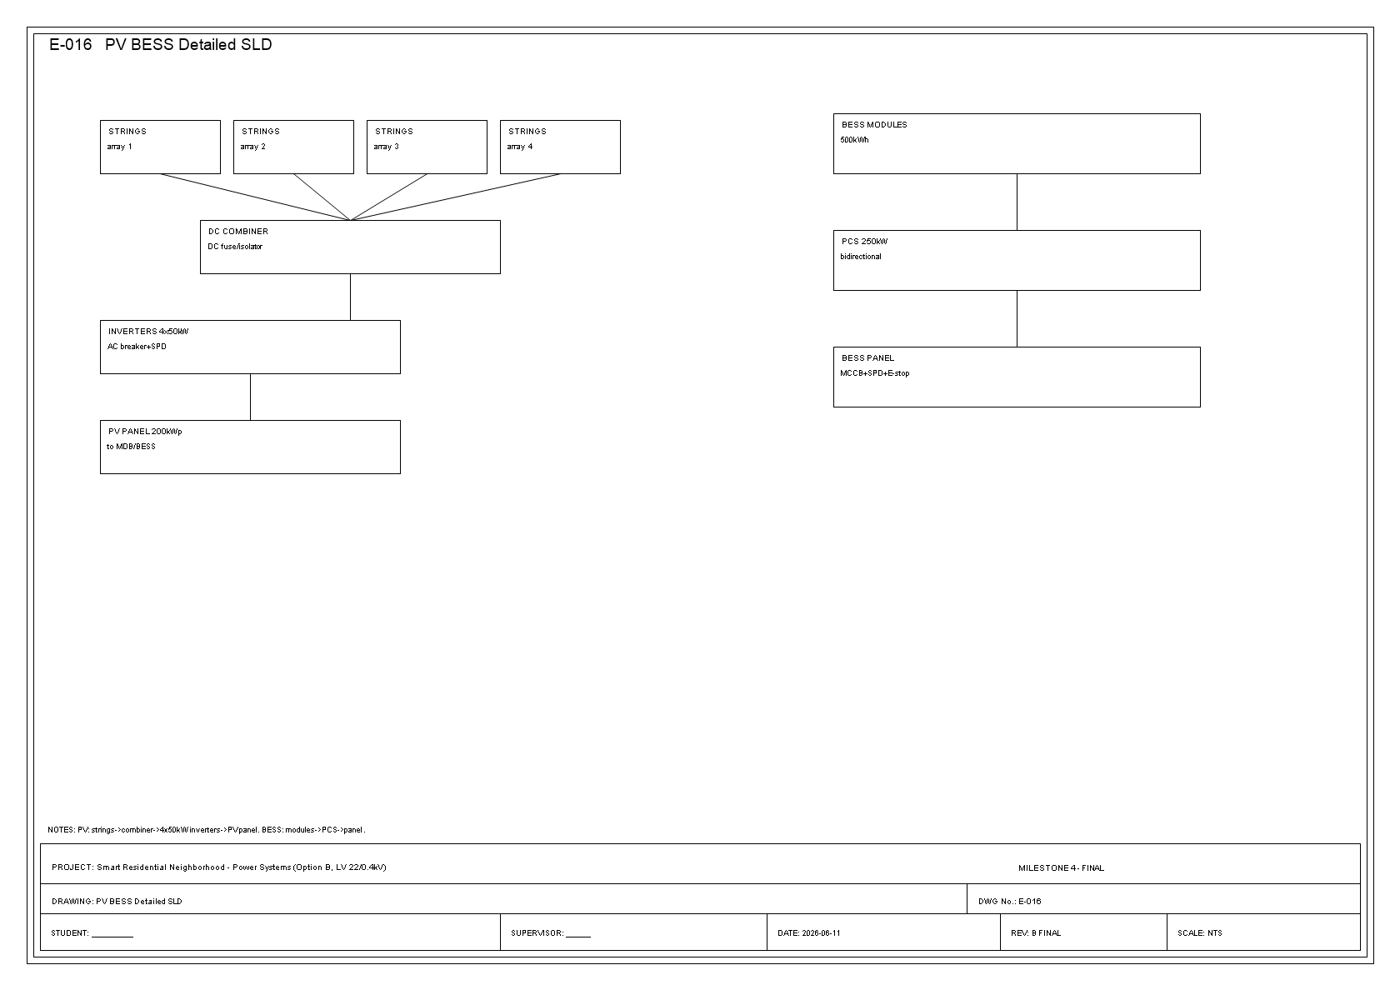
engineering_drawings/PNG/E-016_PV_BESS_Detailed_SLD.png
