MHMADYHYA/smart-neighborhood-power-system-design/engineering_drawings/PNG/E-017_Capacitor_Bank_PF_Correction.png

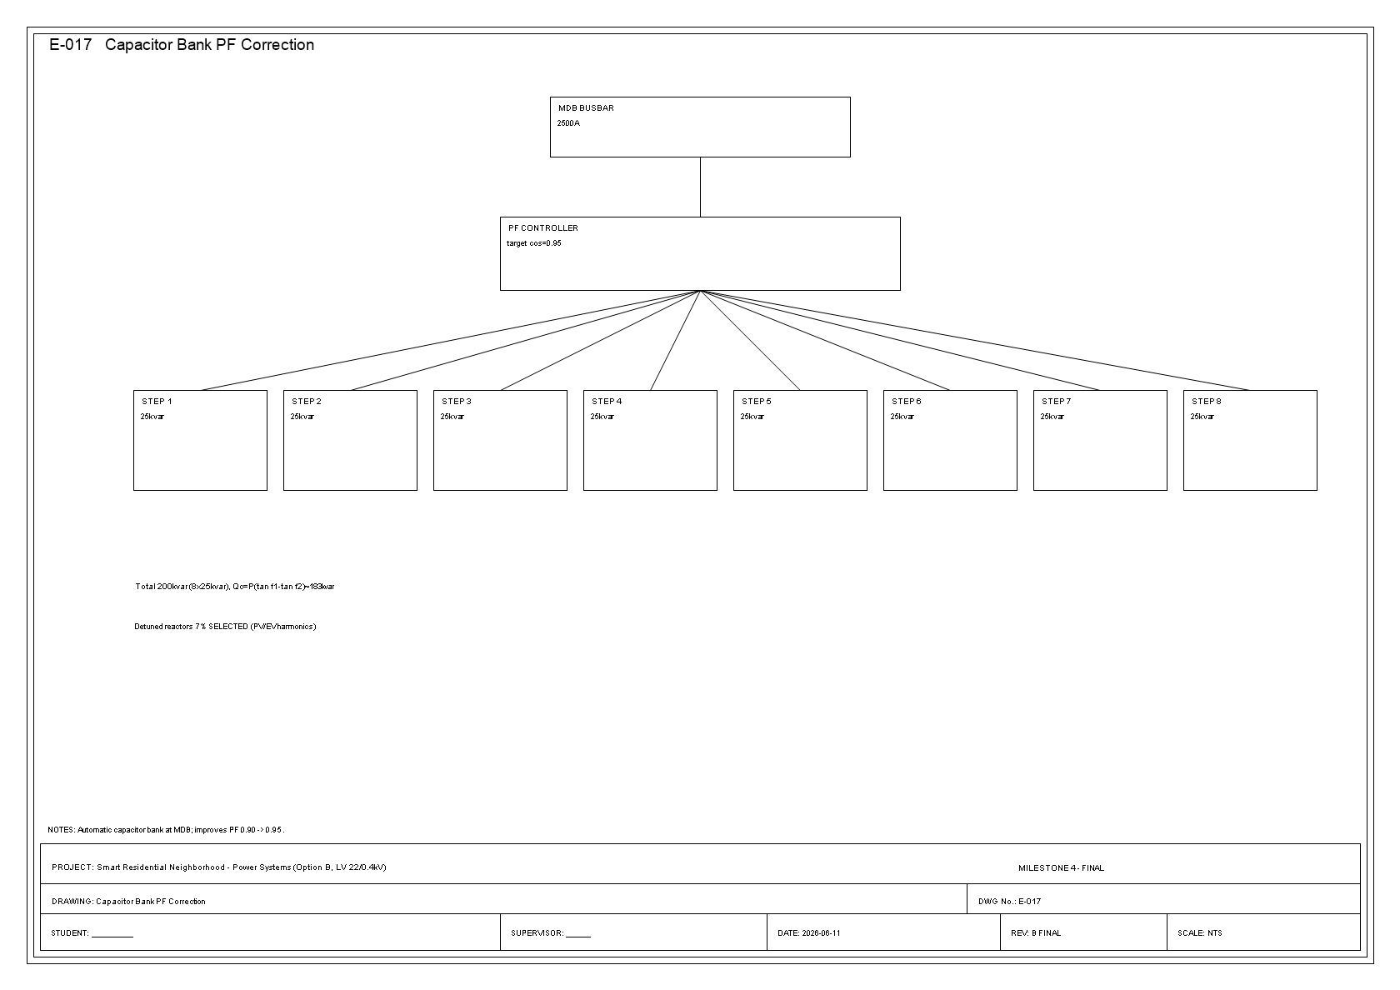
engineering_drawings/PNG/E-017_Capacitor_Bank_PF_Correction.png
