MHMADYHYA/smart-neighborhood-power-system-design/engineering_drawings/PNG/E-018_Short_Circuit_Path_To_End_User.png

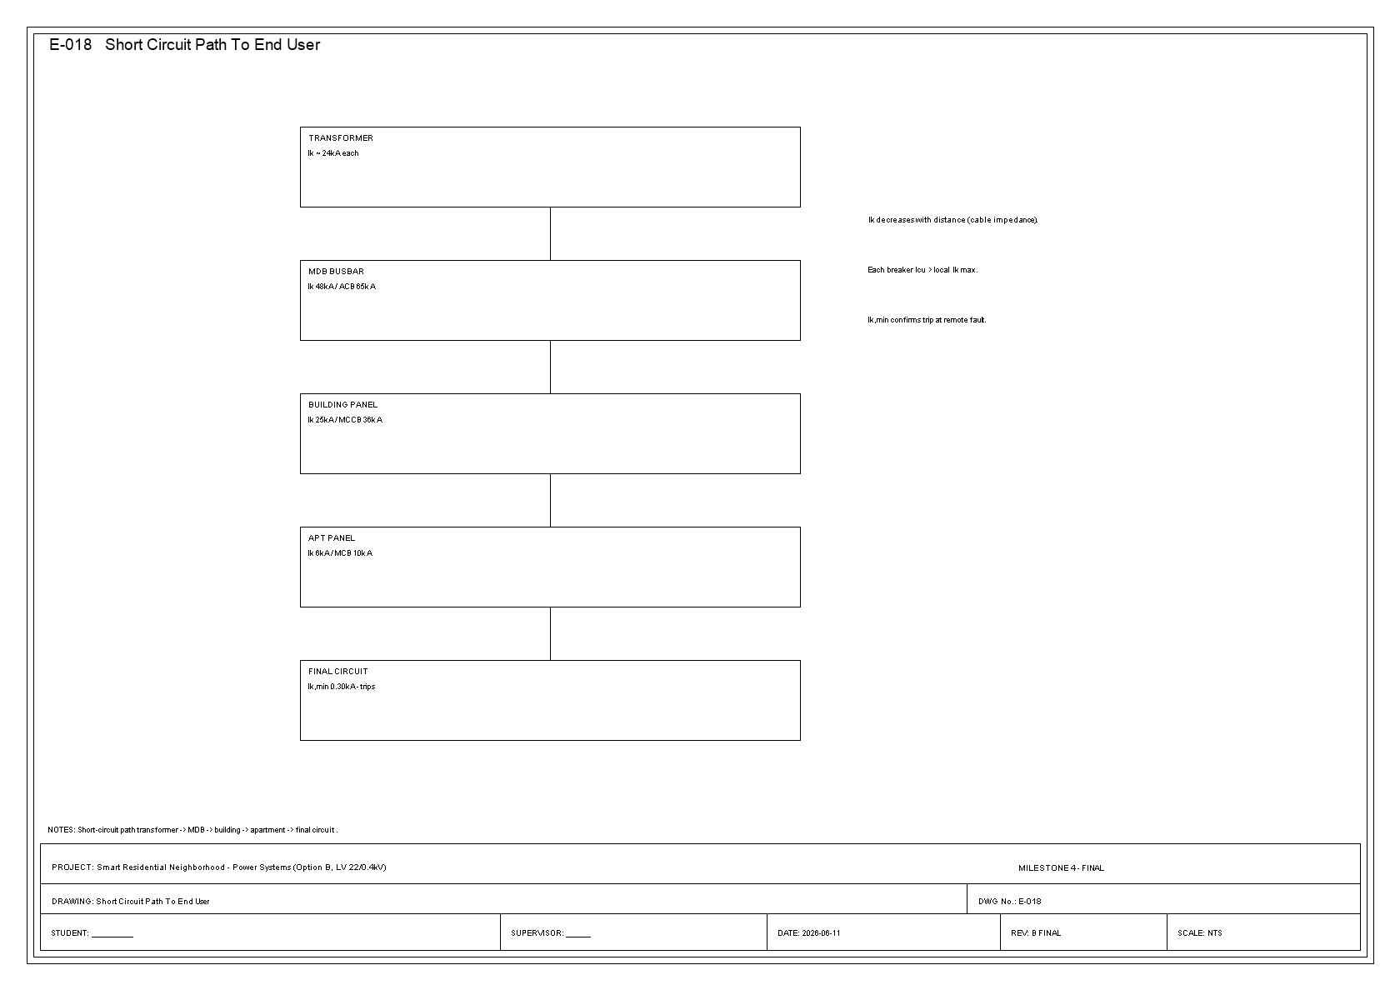
engineering_drawings/PNG/E-018_Short_Circuit_Path_To_End_User.png
