MHMADYHYA/smart-neighborhood-power-system-design/engineering_drawings/DXF/BV-01_Building_LV_Distribution.dxf

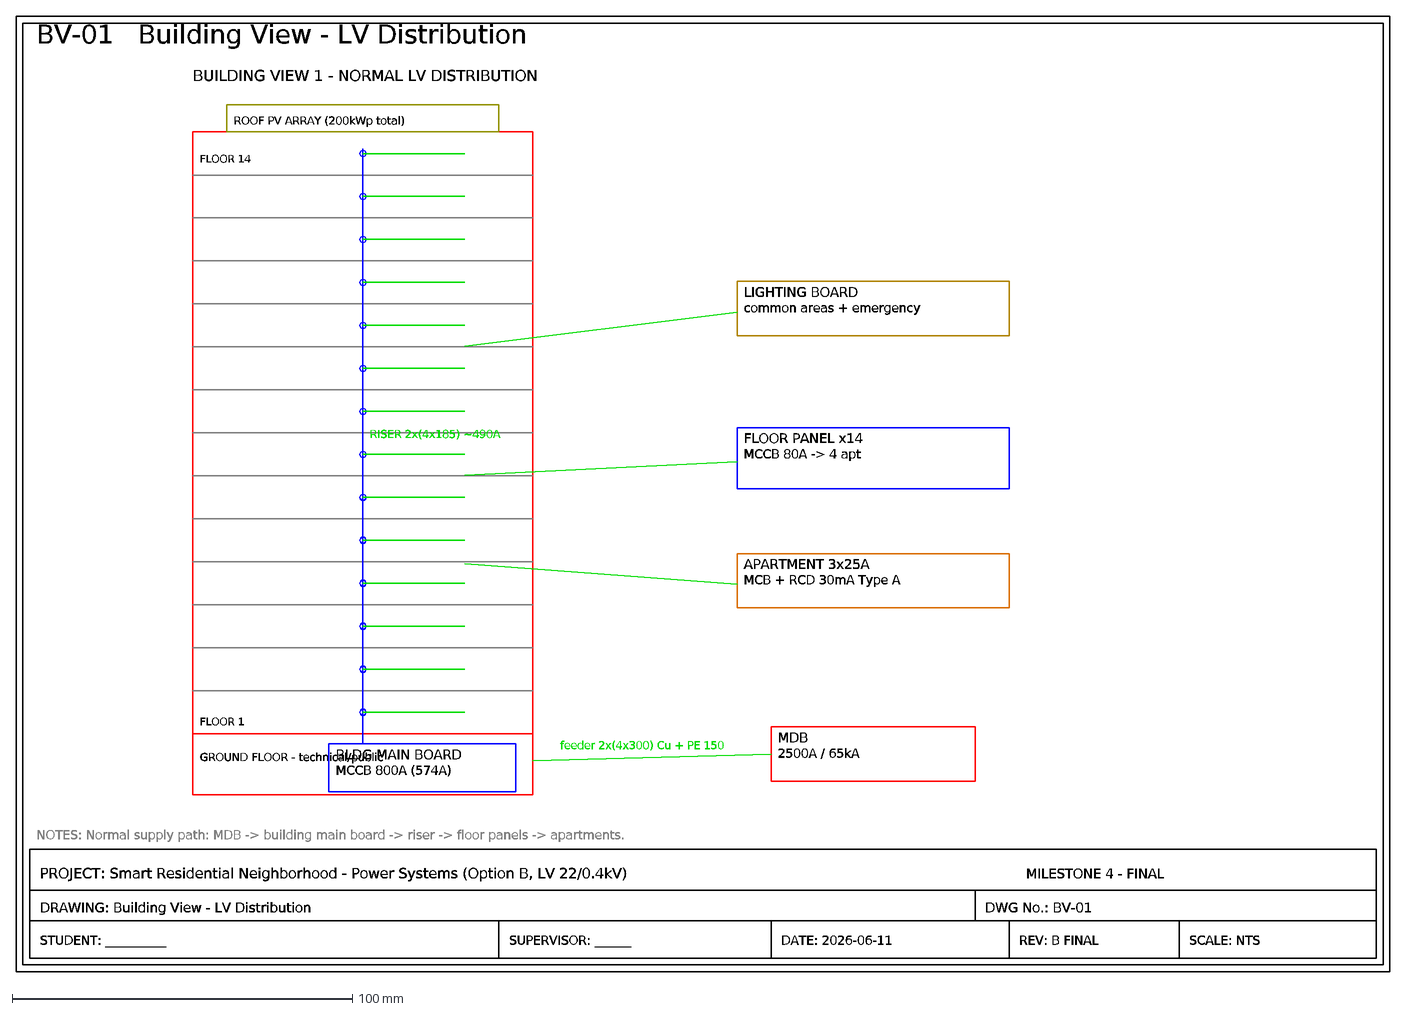
[picture p205: CAD file, 2026-07-05]
engineering_drawings/DXF/BV-01_Building_LV_Distribution.dxf
BV-01 Building View - LV Distribution
PROJECT: Smart Residential Neighborhood - Power Systems (Option B, LV 22/0.4kV)
MILESTONE 4 - FINAL
DRAWING: Building View - LV Distribution
DWG No.: BV-01
STUDENT: __________
SUPERVISOR: ______
DATE: 2026-06-11
REV: B FINAL
SCALE: NTS
ROOF PV ARRAY (200kWp total)
GROUND FLOOR - technical/public
FLOOR 14
FLOOR 1
BUILDING VIEW 1 - NORMAL LV DISTRIBUTION
MDB
2500A / 65kA
feeder 2x(4x300) Cu + PE 150
BLDG MAIN BOARD
MCCB 800A (574A)
RISER 2x(4x185) ~490A
FLOOR PANEL x14
MCCB 80A -> 4 apt
APARTMENT 3x25A
MCB + RCD 30mA Type A
LIGHTING BOARD
common areas + emergency
NOTES: Normal supply path: MDB -> building main board -> riser -> floor panels -> apartments.
