MHMADYHYA/smart-neighborhood-power-system-design/engineering_drawings/DXF/E-015_EV_Charging_Detailed_SLD.dxf

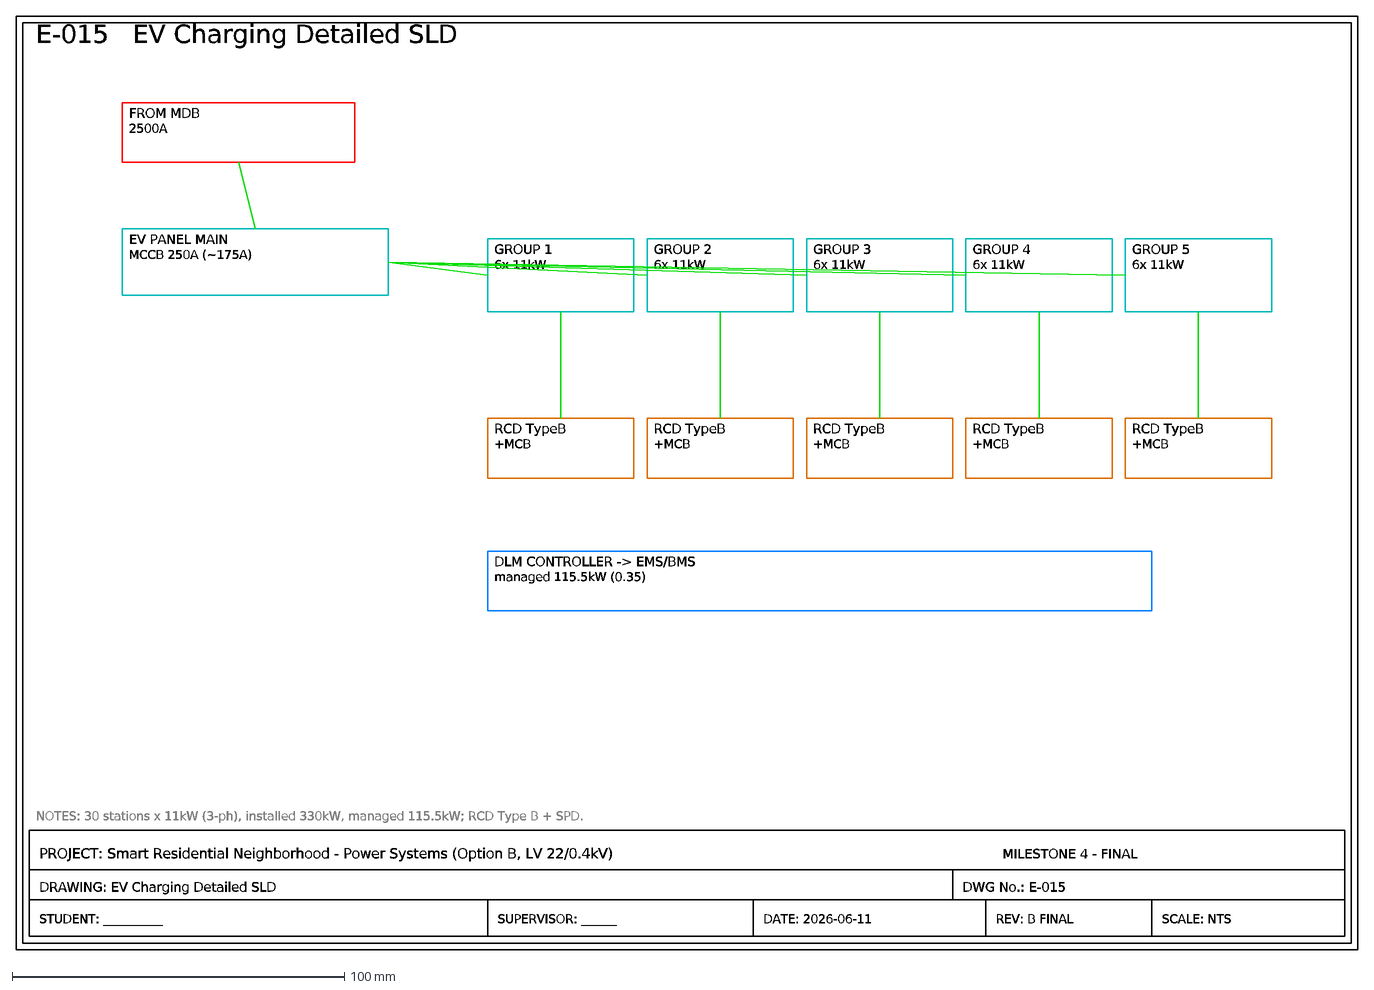
[picture p206: CAD file, 2026-07-05]
engineering_drawings/DXF/E-015_EV_Charging_Detailed_SLD.dxf
E-015 EV Charging Detailed SLD
PROJECT: Smart Residential Neighborhood - Power Systems (Option B, LV 22/0.4kV)
MILESTONE 4 - FINAL
DRAWING: EV Charging Detailed SLD
DWG No.: E-015
STUDENT: __________
SUPERVISOR: ______
DATE: 2026-06-11
REV: B FINAL
SCALE: NTS
FROM MDB
2500A
EV PANEL MAIN
MCCB 250A (~175A)
GROUP 1
6x 11kW
GROUP 2
GROUP 3
GROUP 4
GROUP 5
RCD TypeB
+MCB
DLM CONTROLLER -> EMS/BMS
managed 115.5kW (0.35)
NOTES: 30 stations x 11kW (3-ph), installed 330kW, managed 115.5kW; RCD Type B + SPD.
