MHMADYHYA/smart-neighborhood-power-system-design/engineering_drawings/DXF/E-002_Typical_Building_SLD.dxf

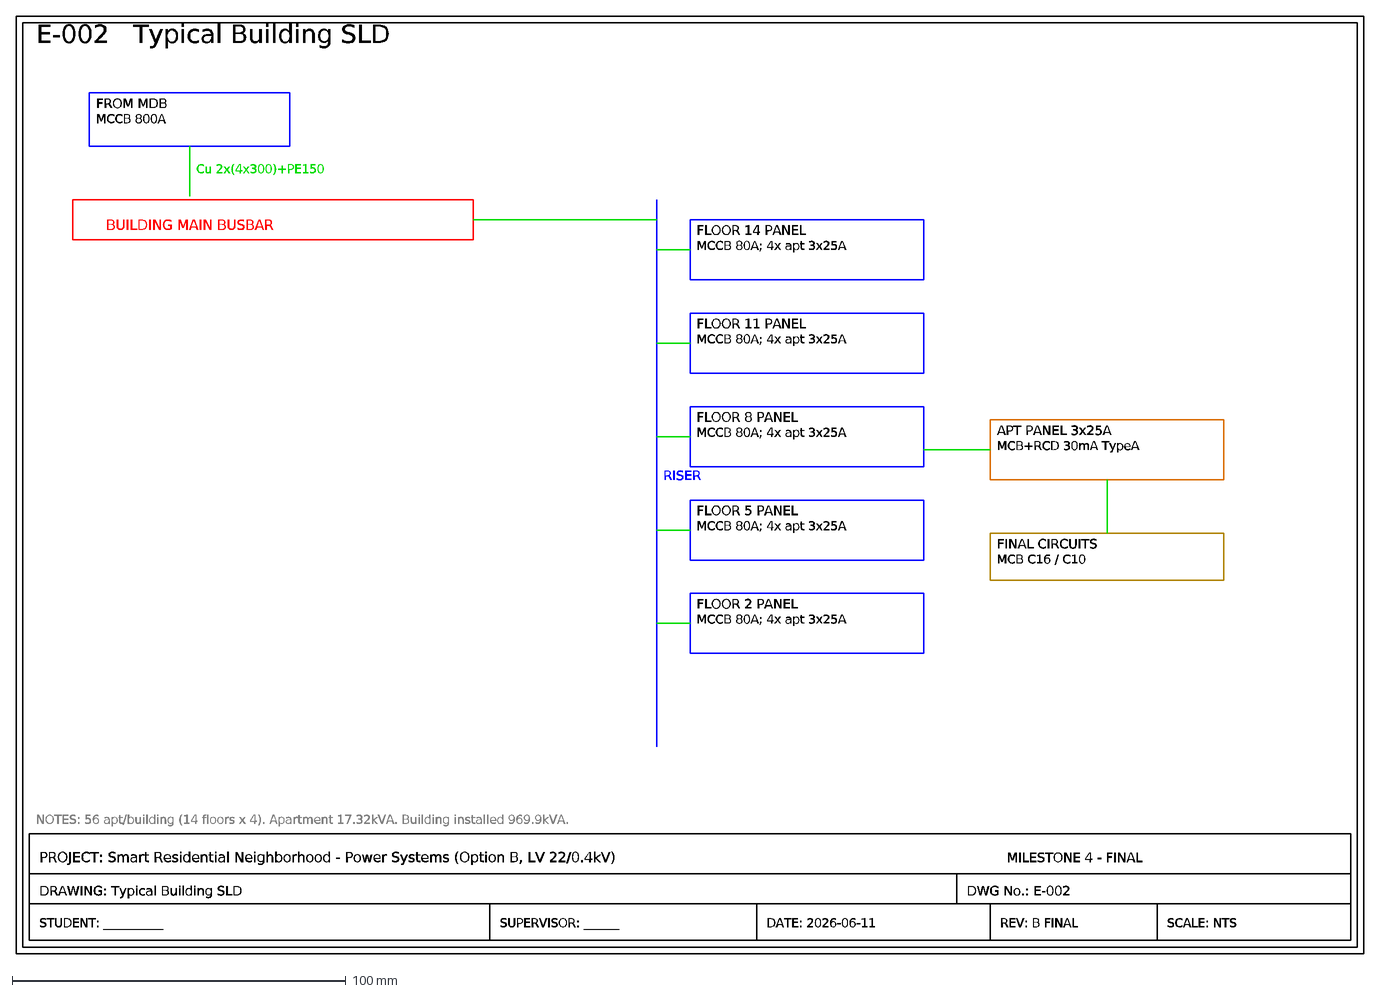
[picture p207: CAD file, 2026-07-05]
engineering_drawings/DXF/E-002_Typical_Building_SLD.dxf
E-002 Typical Building SLD
PROJECT: Smart Residential Neighborhood - Power Systems (Option B, LV 22/0.4kV)
MILESTONE 4 - FINAL
DRAWING: Typical Building SLD
DWG No.: E-002
STUDENT: __________
SUPERVISOR: ______
DATE: 2026-06-11
REV: B FINAL
SCALE: NTS
FROM MDB
MCCB 800A
Cu 2x(4x300)+PE150
BUILDING MAIN BUSBAR
RISER
FLOOR 14 PANEL
MCCB 80A; 4x apt 3x25A
FLOOR 11 PANEL
FLOOR 8 PANEL
FLOOR 5 PANEL
FLOOR 2 PANEL
APT PANEL 3x25A
MCB+RCD 30mA TypeA
FINAL CIRCUITS
MCB C16 / C10
NOTES: 56 apt/building (14 floors x 4). Apartment 17.32kVA. Building installed 969.9kVA.
