MHMADYHYA/smart-neighborhood-power-system-design/engineering_drawings/DXF/E-008_Generator_ATS_UPS_SLD.dxf

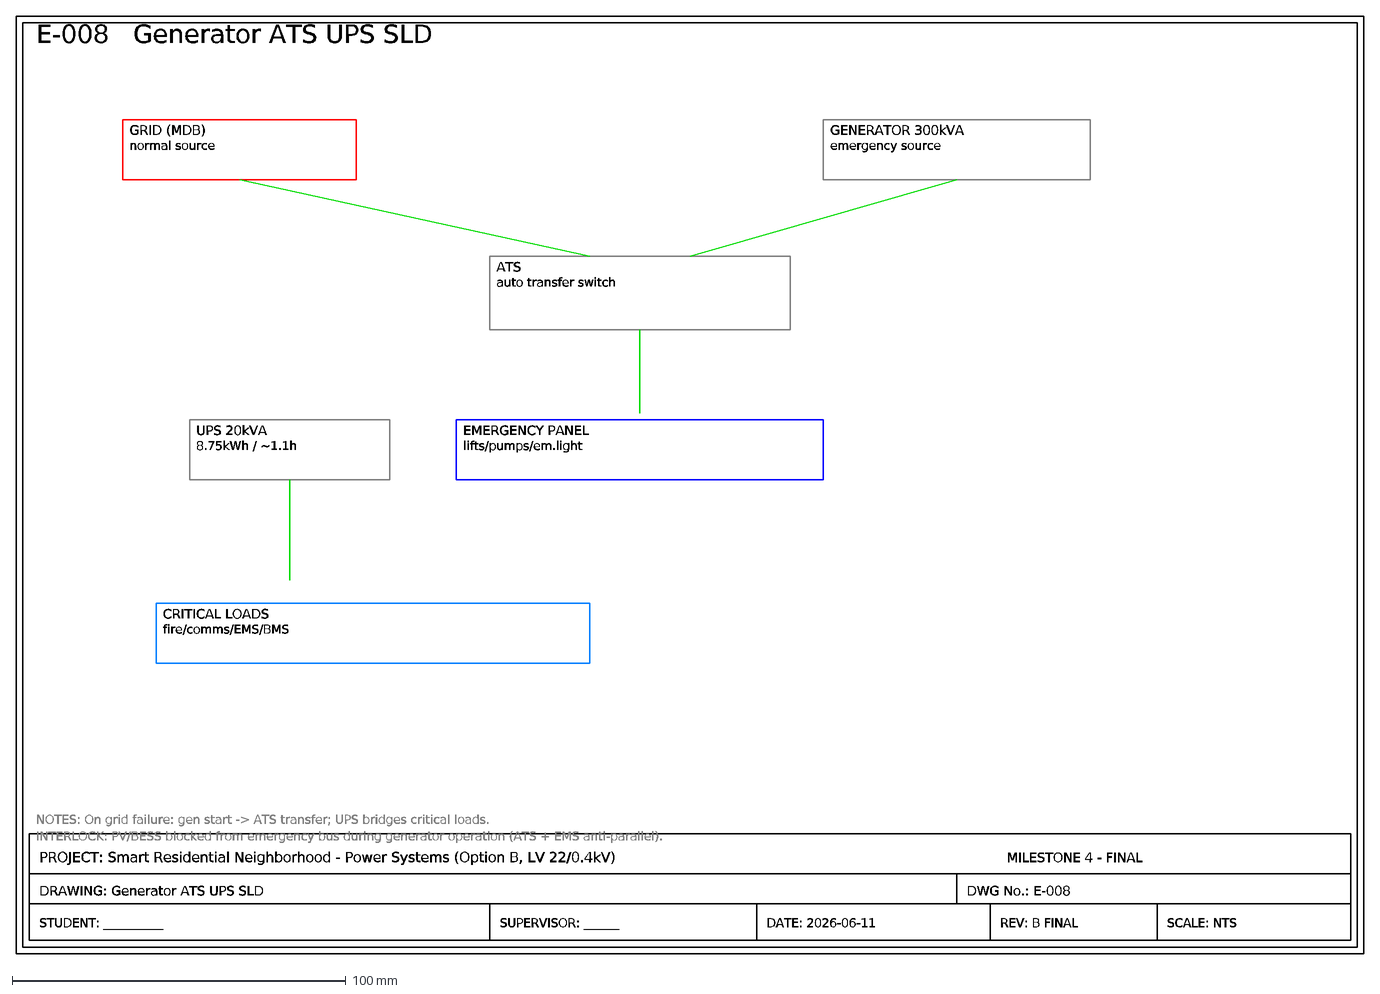
[picture p208: CAD file, 2026-07-05]
engineering_drawings/DXF/E-008_Generator_ATS_UPS_SLD.dxf
E-008 Generator ATS UPS SLD
PROJECT: Smart Residential Neighborhood - Power Systems (Option B, LV 22/0.4kV)
MILESTONE 4 - FINAL
DRAWING: Generator ATS UPS SLD
DWG No.: E-008
STUDENT: __________
SUPERVISOR: ______
DATE: 2026-06-11
REV: B FINAL
SCALE: NTS
GRID (MDB)
normal source
GENERATOR 300kVA
emergency source
ATS
auto transfer switch
EMERGENCY PANEL
lifts/pumps/em.light
UPS 20kVA
8.75kWh / ~1.1h
CRITICAL LOADS
fire/comms/EMS/BMS
NOTES: On grid failure: gen start -> ATS transfer; UPS bridges critical loads.
INTERLOCK: PV/BESS blocked from emergency bus during generator operation (ATS + EMS anti-parallel).
