MHMADYHYA/smart-neighborhood-power-system-design/engineering_drawings/DXF/E-012_EMS_BMS_Architecture.dxf

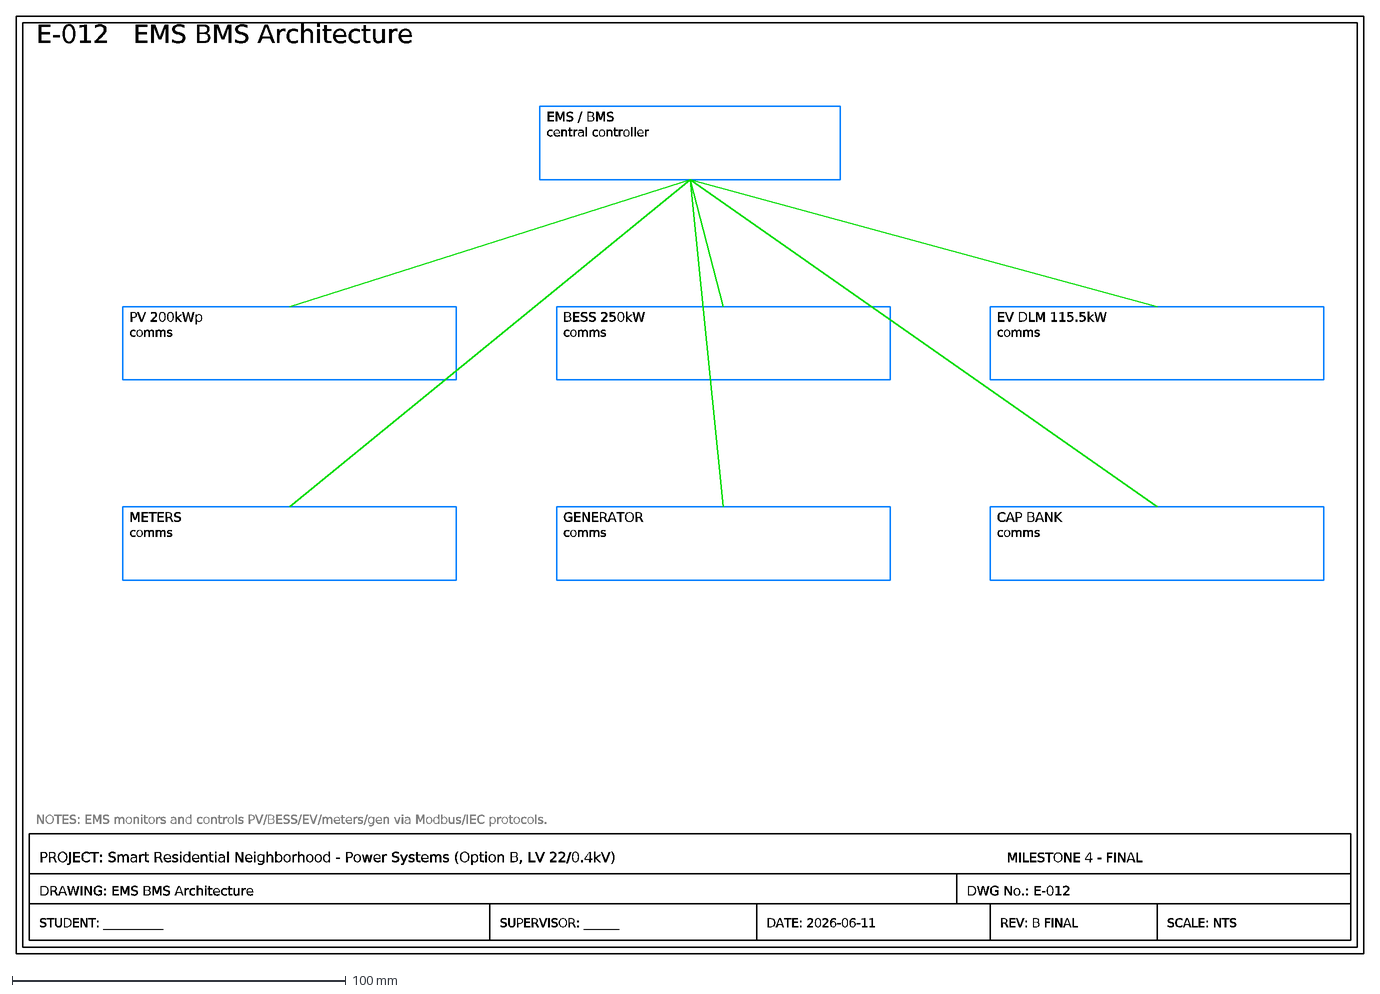
[picture p209: CAD file, 2026-07-05]
engineering_drawings/DXF/E-012_EMS_BMS_Architecture.dxf
E-012 EMS BMS Architecture
PROJECT: Smart Residential Neighborhood - Power Systems (Option B, LV 22/0.4kV)
MILESTONE 4 - FINAL
DRAWING: EMS BMS Architecture
DWG No.: E-012
STUDENT: __________
SUPERVISOR: ______
DATE: 2026-06-11
REV: B FINAL
SCALE: NTS
EMS / BMS
central controller
PV 200kWp
comms
BESS 250kW
EV DLM 115.5kW
METERS
GENERATOR
CAP BANK
NOTES: EMS monitors and controls PV/BESS/EV/meters/gen via Modbus/IEC protocols.
