MHMADYHYA/smart-neighborhood-power-system-design/engineering_drawings/DXF/E-006_Underground_Cable_Routes.dxf

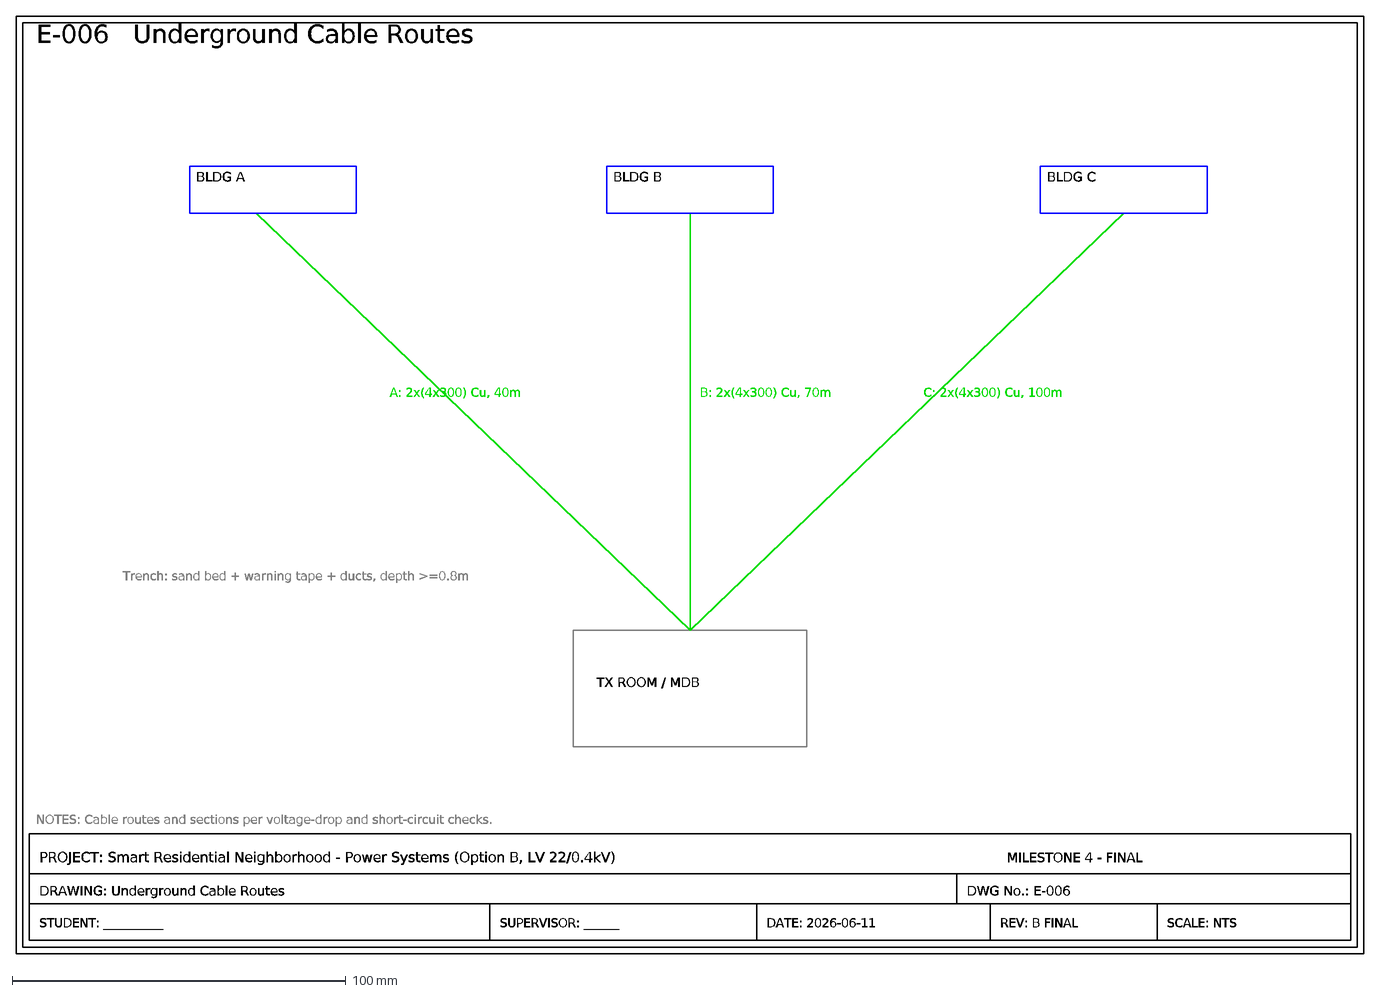
[picture p210: CAD file, 2026-07-05]
engineering_drawings/DXF/E-006_Underground_Cable_Routes.dxf
E-006 Underground Cable Routes
PROJECT: Smart Residential Neighborhood - Power Systems (Option B, LV 22/0.4kV)
MILESTONE 4 - FINAL
DRAWING: Underground Cable Routes
DWG No.: E-006
STUDENT: __________
SUPERVISOR: ______
DATE: 2026-06-11
REV: B FINAL
SCALE: NTS
TX ROOM / MDB
A: 2x(4x300) Cu, 40m
B: 2x(4x300) Cu, 70m
C: 2x(4x300) Cu, 100m
BLDG A
BLDG B
BLDG C
Trench: sand bed + warning tape + ducts, depth >=0.8m
NOTES: Cable routes and sections per voltage-drop and short-circuit checks.
