MHMADYHYA/smart-neighborhood-power-system-design/engineering_drawings/DXF/E-013_Lighting_Emergency_Lighting.dxf

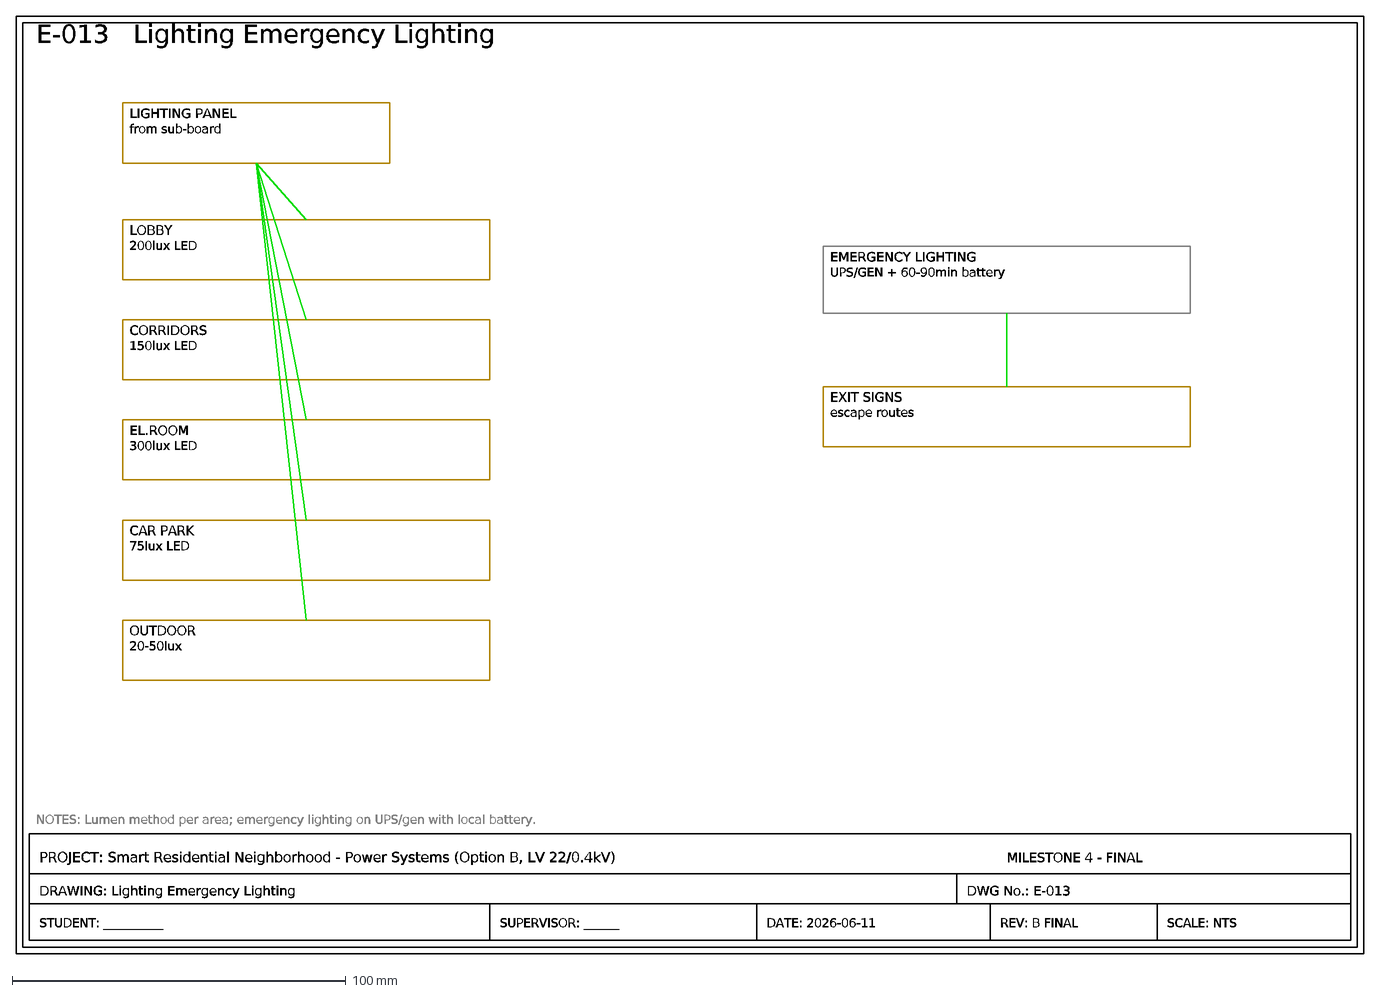
[picture p211: CAD file, 2026-07-05]
engineering_drawings/DXF/E-013_Lighting_Emergency_Lighting.dxf
E-013 Lighting Emergency Lighting
PROJECT: Smart Residential Neighborhood - Power Systems (Option B, LV 22/0.4kV)
MILESTONE 4 - FINAL
DRAWING: Lighting Emergency Lighting
DWG No.: E-013
STUDENT: __________
SUPERVISOR: ______
DATE: 2026-06-11
REV: B FINAL
SCALE: NTS
LIGHTING PANEL
from sub-board
LOBBY
200lux LED
CORRIDORS
150lux LED
EL.ROOM
300lux LED
CAR PARK
75lux LED
OUTDOOR
20-50lux
EMERGENCY LIGHTING
UPS/GEN + 60-90min battery
EXIT SIGNS
escape routes
NOTES: Lumen method per area; emergency lighting on UPS/gen with local battery.
