MHMADYHYA/smart-neighborhood-power-system-design/engineering_drawings/PNG/E-002_Typical_Building_SLD.png

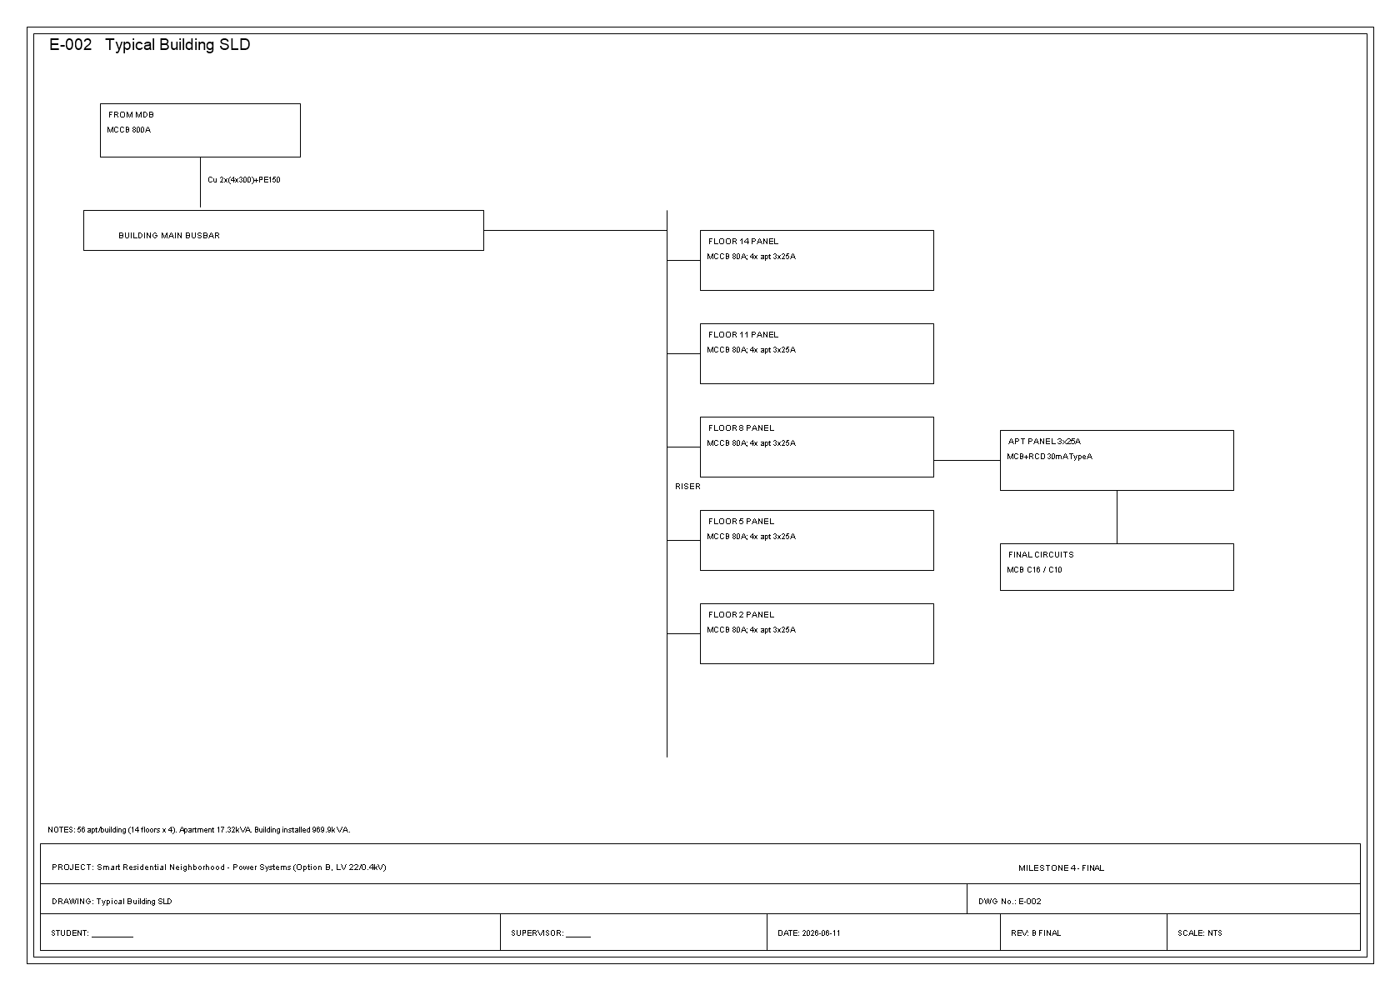
engineering_drawings/PNG/E-002_Typical_Building_SLD.png
